agamrossen/VolAnti/assets/field/104m-unit.jpg

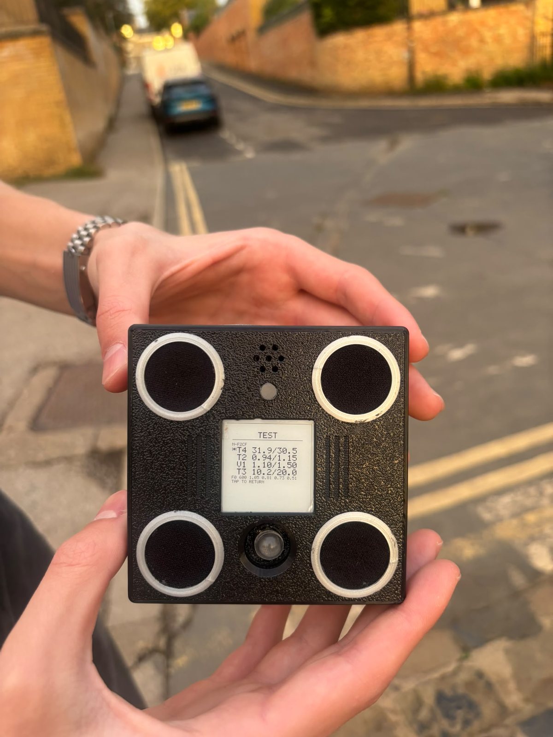
assets/field/104m-unit.jpg
