agamrossen/VolAnti/docs/images/boards-batch.jpg

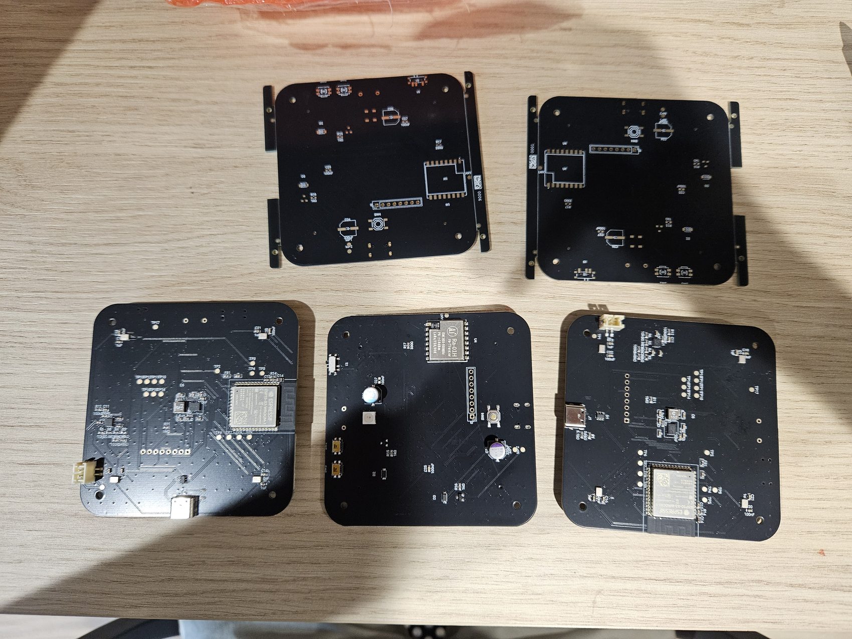
docs/images/boards-batch.jpg
