agamrossen/VolAnti/docs/images/exploded-iso.png

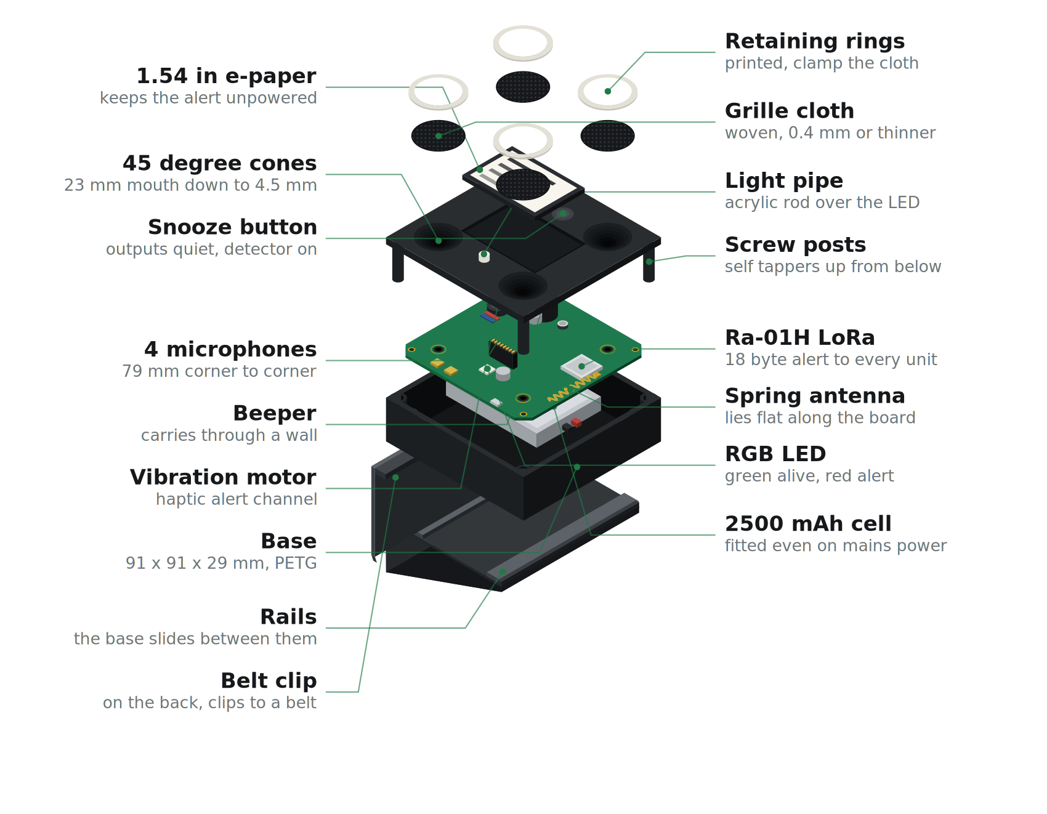
docs/images/exploded-iso.png
