agamrossen/VolAnti/docs/images/hero.jpg

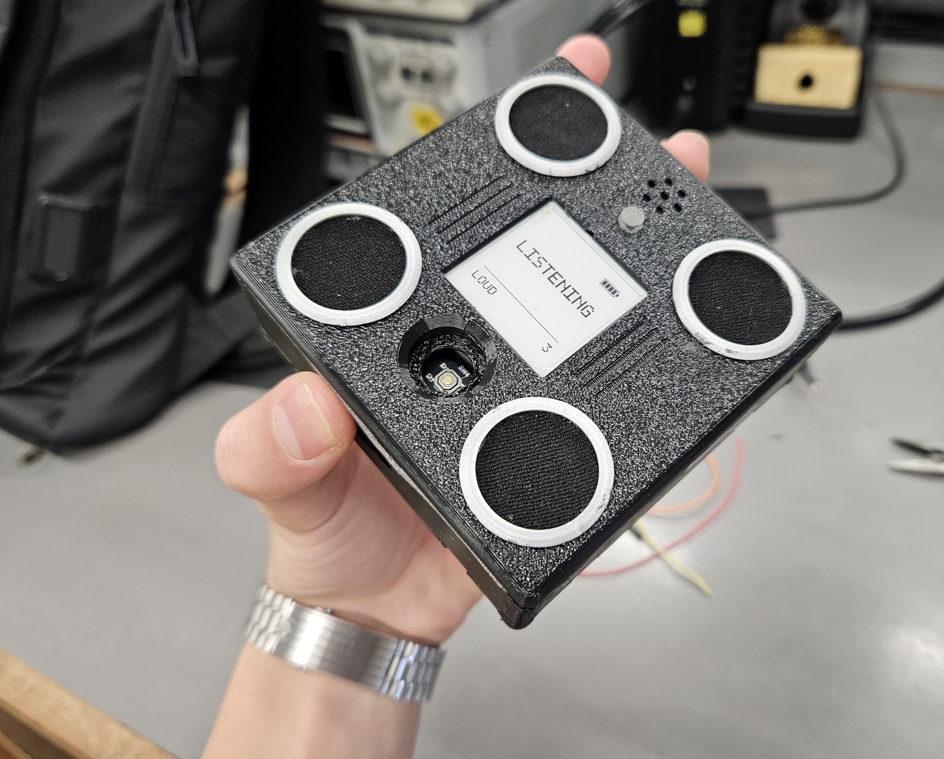
docs/images/hero.jpg
