agamrossen/VolAnti/docs/images/pcb-hand.jpg

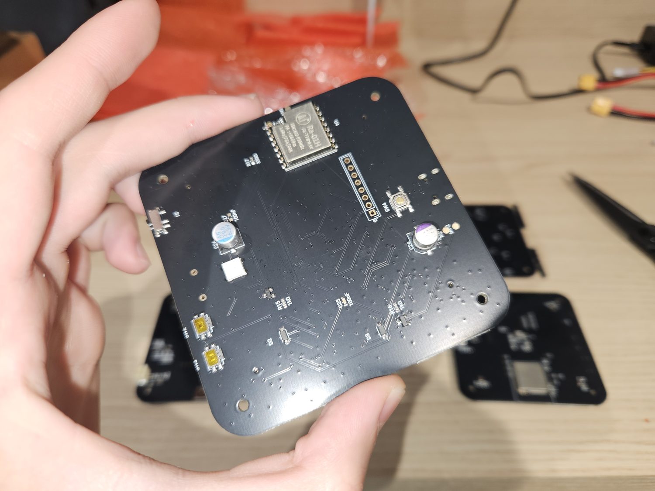
docs/images/pcb-hand.jpg
