agamrossen/VolAnti/firmware/sentry_node/assets/preview_alert.png

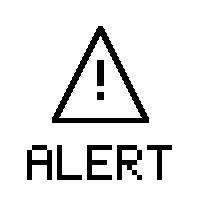
firmware/sentry_node/assets/preview_alert.png
