agamrossen/VolAnti/firmware/sentry_node/assets/preview_alert_wash.png

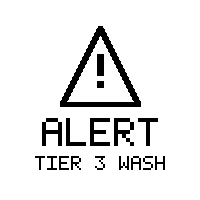
firmware/sentry_node/assets/preview_alert_wash.png
