agamrossen/VolAnti/firmware/sentry_node/assets/preview_listening.png

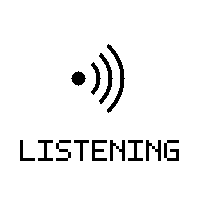
firmware/sentry_node/assets/preview_listening.png
