agamrossen/VolAnti/firmware/sentry_node/assets/preview_listening_footer.png

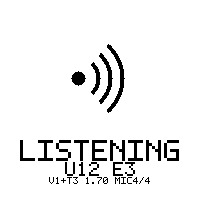
firmware/sentry_node/assets/preview_listening_footer.png
