agamrossen/VolAnti/firmware/sentry_node/assets/preview_listening_footer_rot90.png

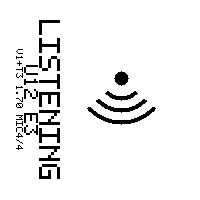
firmware/sentry_node/assets/preview_listening_footer_rot90.png
