agamrossen/VolAnti/firmware/sentry_node/assets/preview_off.png

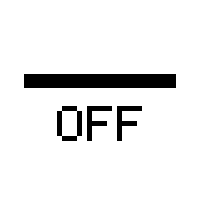
firmware/sentry_node/assets/preview_off.png
