agamrossen/VolAnti/firmware/sentry_node/assets/preview_ready.png

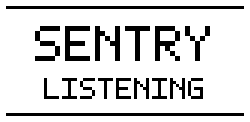
firmware/sentry_node/assets/preview_ready.png
