agamrossen/VolAnti/firmware/sentry_node/assets/preview_rot90_alert.png

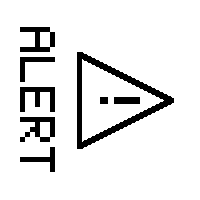
firmware/sentry_node/assets/preview_rot90_alert.png
