agamrossen/VolAnti/firmware/sentry_node/assets/preview_rot90_off.png

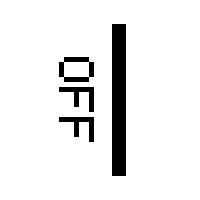
firmware/sentry_node/assets/preview_rot90_off.png
