agamrossen/VolAnti/hardware/enclosure/renders/VolAnti_Base.png

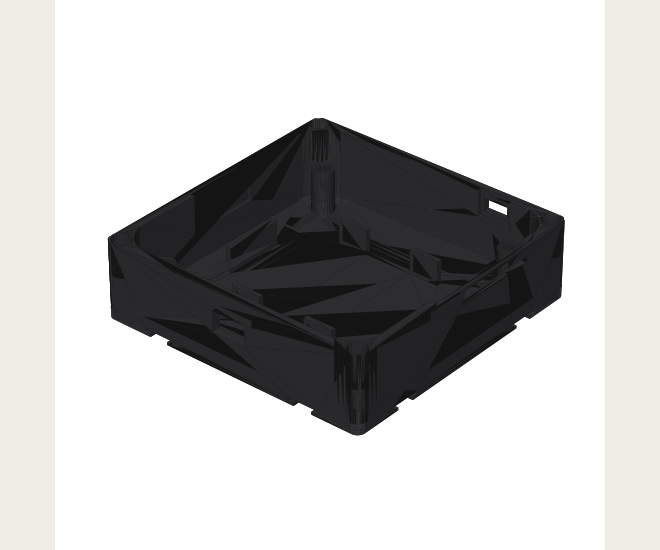
hardware/enclosure/renders/VolAnti_Base.png
