agamrossen/VolAnti/hardware/enclosure/renders/VolAnti_Lid.png

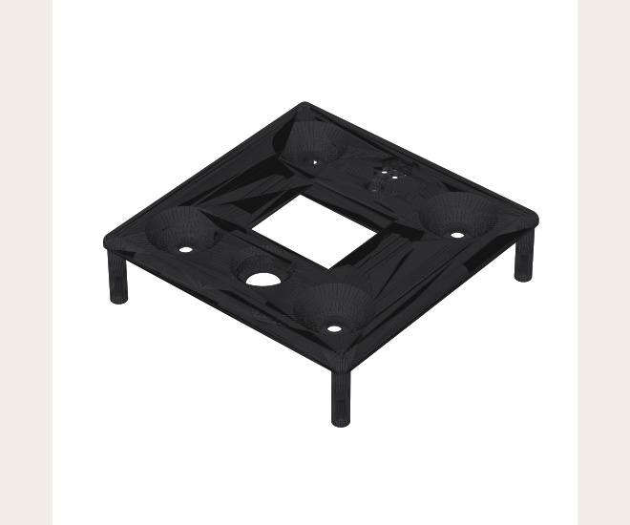
hardware/enclosure/renders/VolAnti_Lid.png
