agamrossen/VolAnti/hardware/enclosure/renders/VolAnti_Mount.png

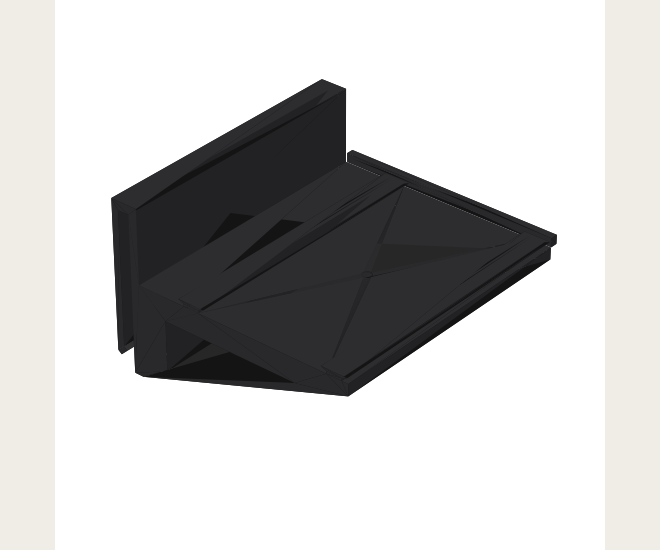
hardware/enclosure/renders/VolAnti_Mount.png
