agamrossen/VolAnti/firmware/sentry_node/assets/preview_rot90_test.png

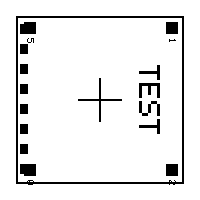
firmware/sentry_node/assets/preview_rot90_test.png
