agamrossen/VolAnti/firmware/sentry_node/assets/preview_test.png

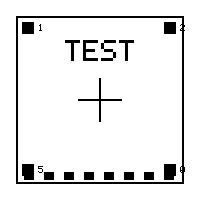
firmware/sentry_node/assets/preview_test.png
