agamrossen/VolAnti/firmware/sentry_node/main/sentry_node.c

/*
 * sentry_node.c - the frame loop, the modes, and the console.
 *
 * For the golden replay the device holds the vectors and the detector and
 * nothing else. It does not hold the expected outcomes: those live in
 * data/golden_vectors.json and are applied by the host comparator, because
 * firmware that knows the answer cannot be said to have reproduced it.
 *
 * Host protocol (line commands in, binary records out):
 *     I                       identity / sizes / free heap, as text
 *     R <idx>                 replay vector idx, stream the trace
 *     P <idx> <from> <to>     ... and interleave forensic probe records
 * Every run emits: header, one record per frame, sentinel.
 */

#include <stdio.h>
#include <stdlib.h>
#include <string.h>

#include "esp_heap_caps.h"
#include "esp_log.h"
#include "esp_sleep.h"
#include "esp_system.h"
#include "esp_timer.h"
#include "freertos/FreeRTOS.h"
#include "freertos/task.h"

#include <math.h>

#include "dsps_fft2r.h"
#include "dsps_fft4r.h"

#include "driver/gpio.h"
#include "driver/rtc_io.h"
#include "esp_adc/adc_cali.h"
#include "esp_adc/adc_cali_scheme.h"
#include "esp_adc/adc_oneshot.h"

#include "actuators.h"
#include "alert_ui.h"
#include "board_pins.h"
#include "boot_rec.h"
#include "combiners_cx.h"
#include "detector.h"
#include "detector_t2.h"
#include "detector_t3.h"
#include "detector_t4.h"
#include "epaper.h"
#include "epaper_draw.h"
#include "ui_config.h"
#include "event_log.h"
#include "settings.h"
#include "led_ws2812.h"
#include "lora_link.h"
#include "mic_cal.h"
#include "nf_probe.h"
#include "power_mon.h"
#include "source.h"
#include "source_i2s_quad.h"
#include "trace.h"

static detector_state_t *g_st;
static detector_work_t  *g_w;
/* The mono staging pair, and why it is not allocated at boot.
 *
 * 12 KB: one n_fft window of float32 and one of int16. Only the mono modes
 * touch it - the golden replay, the meter, the tone check, the self-tests -
 * and the quad pipeline has its own per-channel windows and never reads
 * either.
 *
 * Held for the life of the device it is free only while nothing else is
 * competing: the quad guard needs 70 KB, Tier-2 24 KB, Tier-3 13 KB and the
 * two I2S buses take 48 KB of DMA, and 12 KB held for a mode that is not
 * running is the difference between Tier-3 fitting and the guard refusing to
 * start. So it is allocated lazily and handed back when the guard starts. */
static float            *g_block;      /* sliding window, n_fft float32 */
static int16_t          *g_q;          /* int16 staging, n_fft */

static bool mono_alloc(void)
{
    if (!g_block) {
        g_block = heap_caps_calloc(CFG_N_FFT, sizeof(float),
                                   MALLOC_CAP_INTERNAL | MALLOC_CAP_8BIT);
    }
    if (!g_q) {
        g_q = heap_caps_calloc(CFG_N_FFT, sizeof(int16_t),
                               MALLOC_CAP_INTERNAL | MALLOC_CAP_8BIT);
    }
    if (g_block && g_q) {
        return true;
    }
    trace_text("ERR out of RAM for the mono staging buffers\n");
    return false;
}

static void mono_free(void)
{
    free(g_block);
    g_block = NULL;
    free(g_q);
    g_q = NULL;
}

/* One line of heap truth. Printed when a run starts and when one cannot. */
static void heap_line(const char *what)
{
    char b[96];
    snprintf(b, sizeof(b), "heap %s: free=%u largest=%u\n", what,
             (unsigned)heap_caps_get_free_size(MALLOC_CAP_INTERNAL),
             (unsigned)heap_caps_get_largest_free_block(MALLOC_CAP_INTERNAL));
    trace_text(b);
}

static int cmp_u32(const void *a, const void *b)
{
    uint32_t x = *(const uint32_t *)a, y = *(const uint32_t *)b;
    return (x > y) - (x < y);
}

/* x = q / 32767.0f, exactly as make_golden.py quantised it - 32767, not
 * 32768 - and computed in float32, because numpy's `q.astype(np.float32) /
 * 32767.0` is a float32 operation under NEP 50 weak-scalar promotion. */
static inline float q_to_f(int16_t q)
{
    return (float)q / 32767.0f;
}

/* ==========================================================================
 * One frame loop, four modes. The golden replay and the live microphone run
 * the same code over the same source_read() abstraction; if they did not, the
 * golden evidence would say nothing about the live path, which is the whole
 * point of having the abstraction.
 *
 * The only per-mode differences are which records are emitted and when the
 * loop stops. Nothing mode-specific touches the detector.
 * ========================================================================== */

/* ==========================================================================
 * Tier-2. Everything below is opt-in and reached only through the `H` and
 * `K` letters.
 *
 * The rule that makes it safe: `guard_t2_opts_t *t2o == NULL` is the
 * tier-free behaviour, and every Tier-2 line inside run_quad_pipeline is
 * inside an `if (t2o ...)`. `G` and `Z` pass NULL, so their path through the
 * loop carries the same instructions it would with no Tier-2 in the tree,
 * which is why the golden gate still says what it says.
 * ========================================================================== */
typedef struct {
    bool     enable;
    t2_cfg_t cfg;
    char     cx;              /* 'a' (default) | 'b' | 'c' | 'd' */
    float    f_split_hz;      /* CX-C only */
    float    busoff;          /* CX-D only, samples of bus-B lag */
} guard_t2_opts_t;

/* The runtime exclusion list, set by `E` and consumed by `H`/`K`. Module
 * scope because it must SURVIVE between commands - the operator types it once
 * after a quiet baseline and then runs the guard. */
static int    g_excl_n;
static double g_excl_c[T2_MAX_EXCL];
static double g_excl_t[T2_MAX_EXCL];

static t2_state_t *g_t2st;
static t2_work_t  *g_t2w;
static cx_work_t  *g_cxw;

/* ==========================================================================
 * Tier-3, the wash tier.
 *
 * v1 and Tier-2 search 200-800 Hz for a harmonic comb. The only real propeller
 * this project has recorded put +0.3 dB there and +14.9 dB above 3.2 kHz, and
 * both comb tiers raised zero events on it at 4 m and at 10 m. Tier-3
 * demodulates the high band and finds the blade-pass periodicity in the
 * envelope; on that same audio it latched 94% of the 4 m capture. It is the
 * only tier here that has detected a real rotor.
 *
 * What is wrong with it, equally plainly: it fires on box fans, HVAC
 * condensers, insects, tracked vehicles and helicopters, because a fan and a
 * rotor are the same machine and the statistic cannot separate them. Its
 * calibration failed - the best weighted false-alarm rate reachable at any
 * threshold was 4.87/h against an allowance of 0.40/h - which is why
 * T3_ENABLED_DEFAULT is 0 in the generated header and the no-regression
 * certificate asserts it.
 *
 * It is enabled at runtime rather than in the header, so the sealed artifacts
 * stay untouched and a typed argument or a persisted setting turns it on. The
 * standing rule is that miss cost far exceeds false-alarm cost. Expect
 * nuisance alarms outdoors - that expectation is measured, not speculative -
 * and read the tier field on every alert before believing any of them.
 * ========================================================================== */
typedef struct {
    bool     enable;
    t3_cfg_t cfg;
} guard_t3_opts_t;

/* ==========================================================================
 * Tier-4, the slow comb. Same contract as Tier-3: additive, opt-in, and
 * disabled in the generated header.
 *
 * It is not disabled because it failed. tau4 = 30.5 gives zero events on
 * every real drone-free recording this project owns - 487 s of it, indoor and
 * outdoor - while both real in-band positives fire, the first at 4.45 s. What
 * it does not have is hours. Zero events in 487 s bounds the false-alarm rate
 * at 22/h with 95% confidence against an allowance of 0.40/h, so turning it
 * on in the field means shipping a tier whose false-alarm rate is unmeasured
 * to within a factor of fifty.
 *
 * Until those hours exist it runs on demand, its verdict goes in the trace and
 * the event ring beside the other three, and nothing about the alarm depends
 * on it.
 * ========================================================================== */
typedef struct {
    bool     enable;
    t4_cfg_t cfg;
} guard_t4_opts_t;

static t4_state_t *g_t4st;

static t3_state_t *g_t3st;

/* Tier-3's state is claimed early rather than per-run, and the reason is
 * placement rather than lifetime.
 *
 * t3_state_t is 12688 bytes and must be contiguous. By the time a run has
 * started two I2S buses (48 KB taken as twenty-four separate 2 KB descriptor
 * buffers), the guard (70 KB) and Tier-2 (24 KB), the heap holds 18616 bytes
 * free in no block larger than 7680 - so the allocation fails with plenty of
 * total memory left. Claiming it out of a pristine heap costs the mono modes
 * 12.7 KB they have to spare and removes the failure entirely.
 *
 * Nothing about it is per-run: t3_reset() clears it at the start of every run,
 * exactly as t2_state_reset() does for a buffer that is reallocated. */
static bool t3_boot_alloc(void)
{
    if (g_t3st) {
        return true;
    }
    if (t3_init() != 0) {
        trace_text("ERR t3_init failed (esp-dsp fft2r for the 1024-pt "
                   "envelope transform)\n");
        return false;
    }
    g_t3st = heap_caps_calloc(1, sizeof(t3_state_t),
                              MALLOC_CAP_INTERNAL | MALLOC_CAP_8BIT);
    return g_t3st != NULL;
}

/* Release it again when the configured pair does not include Tier-3.
 *
 * Holding Tier-3's 12688 bytes permanently makes the v1 + Tier-2 pair
 * unallocatable: Tier-2 asks for 15924 with 20720 free and 10752 in the
 * largest block, so the device falls back to v1 alone and the calibrated pair
 * becomes unreachable.
 *
 * So the claim follows the configuration rather than the boot. It is still
 * taken from a pristine heap - reconciled in run_standalone() before the I2S
 * buses and the guard buffers fragment anything - which is the property that
 * matters; what changes is that a pair which does not want it does not pay
 * for it. */
static void t3_free(void)
{
    free(g_t3st);
    g_t3st = NULL;
}

static bool t3_alloc(void) { return g_t3st != NULL; }

static void t4_free(void)
{
    free(g_t4st);
    g_t4st = NULL;
}

/* Idempotent, and claimed from the same pristine heap as the others. ~10 KB,
 * almost all of it the four sub-block accumulators. */
static bool t4_alloc(void)
{
    if (!g_t4st) {
        g_t4st = heap_caps_calloc(1, sizeof(t4_state_t),
                                  MALLOC_CAP_INTERNAL | MALLOC_CAP_8BIT);
    }
    return g_t4st != NULL;
}

static void t2_free(void)
{
    free(g_t2st);
    g_t2st = NULL;
    free(g_t2w);
    g_t2w = NULL;
    free(g_cxw);
    g_cxw = NULL;
}

/* Idempotent, so the same function serves the boot reservation and the lab
 * modes that start a run without one. ~24 KB in two blocks - a t2_work_t is
 * 15924 bytes on its own, and that single block is what fails whenever Tier-2
 * cannot start - plus ~8 KB more only if a non-default combiner is selected.
 *
 * When it is called matters more than what it asks for. Called after the I2S
 * buses and the guard buffers, the 15924 has to come out of a heap already
 * cut into pieces by a 32800-byte spectra block and two DMA rings, and it does
 * not fit with 20720 bytes still free. run_standalone() calls this before any
 * of that; see the reservation block there. */
static bool t2_alloc(bool need_cx)
{
    if (!g_t2st) {
        g_t2st = heap_caps_calloc(1, sizeof(t2_state_t),
                                  MALLOC_CAP_INTERNAL | MALLOC_CAP_8BIT);
    }
    if (!g_t2w) {
        g_t2w = heap_caps_calloc(1, sizeof(t2_work_t),
                                 MALLOC_CAP_INTERNAL | MALLOC_CAP_8BIT);
    }
    if (need_cx && !g_cxw) {
        g_cxw = heap_caps_calloc(1, sizeof(cx_work_t),
                                 MALLOC_CAP_INTERNAL | MALLOC_CAP_8BIT);
        if (!g_cxw) {
            return false;
        }
    }
    return g_t2st && g_t2w;
}

typedef struct {
    const char *name;
    uint32_t n_samples;      /* 0 = unbounded (live) */
    uint32_t max_frames;     /* 0 = unbounded (live) */
    uint32_t prb_from, prb_to;
    bool     emit_pcm;       /* parity: stream the samples too */
    bool     emit_alert;     /* live/parity: one record on the firing frame */
    bool     stop_on_input;  /* live: any host byte ends the run */
    bool     armed;          /* A mode: drive the actuators from rec.fired */
    /* Opt-in. NULL - which every call site that uses designated initialisers
     * leaves it - is exactly the behaviour with no Tier-2 in the tree. Only
     * `K` sets it. */
    const guard_t2_opts_t *t2;
} stream_opts_t;

/* ---- HOW A STANDALONE RUN IS INTERRUPTED --------------------------------
 * A lab mode stops on ANY host byte, which is fine when a human is driving it
 * and fatal when the device starts its own guard at power-on: the byte that
 * stops the run is the first letter of the command that wanted to replace it,
 * and eating it turns `R 0` into `0`. So a standalone run stops on a WHOLE
 * LINE, which is parked here and dispatched by the main loop untouched. */
static char g_pending[64];
static bool g_have_pending;

/* `S` asks the device to hand itself back to the guard. It has to be honoured
 * from both paths - the console loop, and the line that interrupted a
 * standalone run. Handled in only the first, sending `S` to a device that is
 * already guarding stops the guard, routes the line to dispatch_line() and
 * answers with an unknown-command error, leaving the box in the console doing
 * nothing at all. */
static bool g_want_standalone;

/* Why a run ended. The main loop needs to tell "the host wants the console"
 * from "the operator held the button down". */
#define RUN_END_INPUT     0     /* a host line is waiting in g_pending      */
/* The off ritual: a hold. It draws OFF with the reason under it and then
 * deep-sleeps, or parks on a board that cannot, so the cable can be pulled -
 * or the PCB's slider thrown - against a screen that is telling the truth.
 *
 * There is exactly one ending. Parking in standby with the panel still saying
 * LISTENING is the failure the ritual exists to remove, and a tap-count ritual
 * cannot coexist with paging, since three taps is how an operator reads three
 * pages. */
#define RUN_END_POWER     1     /* the two-second hold                      */
#define RUN_END_COMPLETE  2     /* ran to its length, or could not start    */
/* The cell ran out. Kept apart from RUN_END_POWER because the two lead to
 * different words on the same screen: one is an operator putting the device
 * away, the other is a device that must not come straight back up and finish
 * the battery off. */
#define RUN_END_BATTERY   3

static inline uint32_t now_ms(void)
{
    return (uint32_t)(esp_timer_get_time() / 1000);
}

/* ---- console-transparent commands ---------------------------------------
 *
 * Any host line takes the console and stops the guard. That is deliberate,
 * because a lab session must be deterministic - but it makes two commands
 * impossible to use for what they exist for. `U btn` cannot drive the state
 * machine if the line carrying it stops the machine, and the frame-budget gate
 * needs an alert to land while four tiers are running.
 *
 * So exactly two prefixes are handled in the reader and never reach the
 * take-over. They are the two that act on the running guard rather than
 * asking it to stand down. Everything else takes the console. */
static const char *skip_ws(const char *p);
static void info_publish(int alive, int amb_db, const char *amb_word);
static void test_publish(void);
static void test_console_line(void);
static void frozen_publish(void);
static bool cmd_btn_word(const char *args);
static bool cmd_alert_word(const char *args);

static bool run_transparent_line(const char *line)
{
    const char *a = skip_ws(line);
    if (*a != 'U' && *a != 'u') {
        return false;
    }
    a = skip_ws(a + 1);
    if (!strncmp(a, "btn", 3)) {
        return cmd_btn_word(skip_ws(a + 3));
    }
    if (!strncmp(a, "alert", 5)) {
        return cmd_alert_word(skip_ws(a + 5));
    }
    return false;
}

/* The one place a long run decides to end. Standalone runs consume a whole
 * line and park it; lab runs stop on any byte. */
static bool run_should_stop(bool standalone, bool armed, int *reason)
{
    if (armed && alert_ui_power_off_requested()) {
        *reason = RUN_END_POWER;
        return true;
    }
    /* The rotation an operator just asked for, persisted. Polled beside the
     * power request because they are the same kind of event: a hold on the
     * button that the UI has already acted on and that something outside the
     * UI has to finish. The panel has already turned; this only writes the
     * quadrant to NVS so it survives the next power cycle, which is the whole
     * point of being able to do it without a laptop. Settings deliberately do
     * not reach into alert_ui.c, so the write lives here. */
    if (alert_ui_take_rotation()) {
        settings_mut()->epd_rotation = epaper_get_rotation();
        const bool ok = settings_save();
        char rb[96];
        snprintf(rb, sizeof(rb), "ROT %u deg %s\n",
                 (unsigned)epaper_degrees_from_quadrant(epaper_get_rotation()),
                 ok ? "saved" : "NOT SAVED");
        trace_text(rb);
    }
    /* The cell, checked here beside the button because they are the same kind
     * of event: something outside the detector has decided the run is over.
     * Reading it is a volatile byte load - the measurement happens on the
     * power task, on the other core, once every ten seconds. Inert on any
     * board with no divider, where power_mon_state() returns POWER_OK. */
    if (armed && power_mon_state() == POWER_EMPTY) {
        *reason = RUN_END_BATTERY;
        return true;
    }
    if (standalone) {
        if (trace_try_line(g_pending, sizeof(g_pending)) > 0) {
            /* Handled here and the guard keeps running: see
             * run_transparent_line. */
            if (run_transparent_line(g_pending)) {
                return false;
            }
            g_have_pending = true;
            *reason = RUN_END_INPUT;
            return true;
        }
        return false;
    }
    if (trace_poll_byte() >= 0) {
        *reason = RUN_END_INPUT;
        return true;
    }
    return false;
}

static void run_stream(source_t *src, const stream_opts_t *o)
{
    trace_hdr_t h = {
        .magic = TRACE_MAGIC_HDR, .version = TRACE_VERSION,
        .n_samples = o->n_samples, .n_frames = o->max_frames,
        .threshold = src->thr,   /* the source's own preset, not a global */
        .fs = CFG_FS, .n_fft = CFG_N_FFT, .hop = CFG_HOP,
        .n_bins = CFG_N_BINS, .n_f0 = CFG_N_F0,
        .rec_size = sizeof(trace_rec_t),
    };
    strncpy(h.name, o->name, sizeof(h.name) - 1);
    trace_send_hdr(&h);

    detector_state_reset(g_st, src->thr);
    /* The golden vectors test the sealed detector and nothing else.
     * detector_state_reset() memsets, so trk_family and veto_voice are clear
     * here whatever the operator has stored in settings, and the vectors are
     * replayed against exactly the code they were cut from. That is true only
     * as a side effect of the memset, so: do not copy the settings flags into
     * g_st on this path. A gate that judges a different detector from the one
     * it was calibrated against proves nothing. */
    g_st->trk_family = false;
    g_st->veto_voice = false;
    g_st->nf_gate    = false;   /* same reason */
    const bool t2on = (o->t2 != NULL && o->t2->enable);
    if (t2on) {
        t2_state_reset(g_t2st);
    }
    uint8_t prev_fired2 = 0;
    uint32_t t2_hits_total = 0;

    const bool bounded = (o->max_frames != 0);
    uint32_t *us = bounded ? calloc(o->max_frames, sizeof(uint32_t)) : NULL;
    uint64_t total_us = 0;
    uint32_t max_us = 0, n_fast = 0;
    uint64_t us_fft = 0, us_mag = 0, us_floor = 0, us_score = 0;
    float peak = -1e30f;
    int32_t longest = 0;
    double t_last = 0.0;
    uint32_t i = 0;
    uint8_t prev_fired = 0;
    uint32_t pcm_seq = 0, sample_index = 0;

    for (i = 0; !bounded || i < o->max_frames; i++) {
        /* slide the analysis window: frame i is x[i*hop : i*hop + n_fft] */
        const int want = (i == 0) ? CFG_N_FFT : CFG_HOP;
        if (i != 0) {
            memmove(g_block, g_block + CFG_HOP,
                    (CFG_N_FFT - CFG_HOP) * sizeof(float));
        }
        if (source_read(src, g_q, (size_t)want) != want) {
            break;                   /* stream ended, or the mic stopped */
        }
        float *dst = (i == 0) ? g_block : g_block + (CFG_N_FFT - CFG_HOP);
        for (int k = 0; k < want; k++) {
            dst[k] = q_to_f(g_q[k]);
        }
        if (o->emit_pcm) {
            /* Emitted before the trace record derived from it, and including
             * the whole first window, so the host can reconstruct exactly the
             * sample array the detector saw - x[0 : n_fft + (frames-1)*hop]. */
            trace_send_pcm(pcm_seq++, sample_index, g_q, (uint16_t)want);
        }
        sample_index += (uint32_t)want;

        /* frame END time - causal, exactly as detector.py computes it */
        const double t = (double)(i * CFG_HOP + CFG_N_FFT) / (double)CFG_FS;
        frame_rec_t rec;

        const int64_t c0 = esp_timer_get_time();
        front_end(g_block, g_w->spec[0], g_w);
        const cf32_t *sp = combiner(&g_w->spec[0][0], CFG_N_CHANNELS, g_w);
        const int64_t cf = esp_timer_get_time();
        back_end(sp, g_st, t, i, g_w, &rec);
        const int64_t c1 = esp_timer_get_time();
        us_fft += (uint64_t)(cf - c0);
        us_mag += rec.us_mag;
        us_floor += rec.us_floor;
        us_score += rec.us_score;

        const uint32_t dt = (uint32_t)(c1 - c0);
        if (us) {
            us[i] = dt;
        }
        total_us += dt;
        if (dt > max_us) {
            max_us = dt;
        }
        if (rec.score > peak) {
            peak = rec.score;
        }
        if (rec.chain > longest) {
            longest = rec.chain;
        }
        n_fast += rec.floor_fast;
        t_last = t;

        trace_rec_t r = {
            .magic = TRACE_MAGIC_REC,
            .frame = rec.frame, .t_s = rec.t_s, .score = rec.score,
            .f0_bin = rec.f0_bin, .f0_hz = rec.f0_hz,
            .f0_raw_hz = rec.f0_raw_hz, .teeth = rec.teeth,
            .floor_fast = rec.floor_fast, .reanch = rec.reanch,
            .n_held_bins = rec.n_held_bins, .above_thr = rec.above_thr,
            .cont_accepted = rec.cont_accepted, .chain = rec.chain,
            .fired = rec.fired, .is_octave = rec.is_octave,
            .us_frame = dt,
        };
        trace_send_rec(&r);

        if (o->emit_alert && rec.fired && !prev_fired) {
            trace_alt_t a = {.magic = TRACE_MAGIC_ALT, .frame = i,
                             .t_s = t, .f0_hz = rec.f0_hz,
                             .score = rec.score, .chain = rec.chain,
                             .n_events = (uint32_t)g_st->n_events + 1u};
            trace_send_alt(&a);
        }
        prev_fired = rec.fired;

        /* Tier-2 beside the sealed tier, on the same spectrum, in `K` mode
         * only. It reads `sp` after back_end has finished with it and writes
         * nothing v1 can see, which is why `R` and `K` produce identical v1
         * records for the same vector. */
        if (t2on) {
            t2_rec_t t2r;
            if (t2_step(sp, NULL, 1, &o->t2->cfg, g_t2st, t, i, g_t2w, &t2r)) {
                trace_t2r_t tr = {
                    .magic = TRACE_MAGIC_T2R, .frame = t2r.frame,
                    .t_s = t2r.t_s, .score2 = t2r.score2,
                    .f02_hz = t2r.f02_hz, .f02_row = t2r.f02_row,
                    .teeth2 = t2r.teeth2, .hit = t2r.hit,
                    .fired2 = t2r.fired2, .excluded = t2r.excluded,
                    .hits = t2r.hits, .n2 = t2r.n2,
                    .track_age = t2r.track_age, .kappa = t2r.kappa,
                    .us_t2 = t2r.us_t2};
                trace_send_t2r(&tr);
                t2_hits_total += t2r.hit;
                if (t2r.fired2 && !prev_fired2) {
                    trace_al2_t a2 = {
                        .magic = TRACE_MAGIC_AL2, .frame = i, .t_s = t,
                        .f02_hz = g_t2st->f0_on, .score2 = t2r.score2,
                        .hits = t2r.hits, .kappa = t2r.kappa,
                        .n_events = (uint32_t)g_t2st->n_events + 1u};
                    trace_send_al2(&a2);
                }
                prev_fired2 = t2r.fired2;
            }
        }

        /* The entire armed-mode integration: one O(1) call, reading a flag
         * the detector already computed. It cannot influence front_end,
         * combiner, back_end or their inputs, and it is skipped entirely in
         * every other mode, which is why `L` remains a valid timing comparator
         * for `A`. */
        if (o->armed) {
            alert_ui_tick(rec.fired != 0, ALERT_TIER_V1, now_ms());
        }

        if (i >= o->prb_from && i <= o->prb_to) {
            probe_rec_t p;
            detector_probe(g_w, g_st, &rec, &p);
            trace_prb_t tp = {.magic = TRACE_MAGIC_PRB, .frame = i,
                              .win_checksum = window_checksum(g_w->fftbuf,
                                                              CFG_N_FFT),
                              .e = p.e, .e_slow = p.e_slow, .flat = p.flat,
                              .rising = p.rising, .fast = p.fast,
                              .argmax_bin = p.argmax_bin,
                              .argmax_score = p.argmax_score};
            memcpy(tp.probe_bin, p.probe_bin, sizeof(tp.probe_bin));
            memcpy(tp.probe_mag, p.probe_mag, sizeof(tp.probe_mag));
            memcpy(tp.probe_floor, p.probe_floor, sizeof(tp.probe_floor));
            memcpy(tp.probe_S, p.probe_S, sizeof(tp.probe_S));
            trace_send_prb(&tp);
        }

        if (o->stop_on_input && trace_poll_byte() >= 0) {
            i++;
            break;
        }
    }

    detector_finish(g_st, t_last);
    if (t2on) {
        t2_finish(g_t2st, t_last);
        char b[80];
        snprintf(b, sizeof(b), "T2 events=%u hits=%u\n",
                 (unsigned)g_t2st->n_events, (unsigned)t2_hits_total);
        trace_text(b);
    }

    const uint32_t n_done = i;
    uint32_t p99 = 0;
    if (us && n_done) {
        qsort(us, n_done, sizeof(uint32_t), cmp_u32);
        uint32_t k = (uint32_t)((99 * n_done + 99) / 100);   /* ceil(0.99n) */
        if (k == 0) {
            k = 1;
        }
        p99 = us[k - 1];
    }
    free(us);

    trace_end_t e = {
        .magic = TRACE_MAGIC_END, .n_frames = n_done,
        .verdict_fires = (g_st->n_events > 0) ? 1 : 0,
        .n_events = (uint32_t)g_st->n_events,
        .peak_score = peak, .longest_chain = longest,
        .n_floor_fast = n_fast, .n_reanch = 0, .n_held_frames = 0,
        .total_us = total_us, .max_us = max_us, .p99_us = p99,
        .us_fft = us_fft, .us_mag = us_mag, .us_floor = us_floor,
        .us_score = us_score,
        .chain_overflow = g_st->overflow ? 1 : 0,
    };
    trace_send_end(&e);
}

/* ---- mode: golden - the parity build ----------------------------------- */
static void run_vector(int idx, uint32_t prb_from, uint32_t prb_to)
{
    if (!mono_alloc()) {
        return;
    }
    source_t src;
    if (source_golden(&src, idx) != ESP_OK) {
        trace_text("ERR bad vector index\n");
        return;
    }
    const uint32_t n = src.n_total;
    const stream_opts_t o = {
        .name = src.name, .n_samples = n,
        .max_frames = (n < CFG_N_FFT) ? 0u : 1u + (n - CFG_N_FFT) / CFG_HOP,
        .prb_from = prb_from, .prb_to = prb_to,
    };
    if (o.max_frames == 0) {
        trace_text("ERR vector shorter than one window\n");
        return;
    }
    run_stream(&src, &o);
}

/* ---- mode: K - golden vector i, with Tier-2 running beside it -----------
 *
 * Replays the same vector from the same flash array through the same
 * run_stream at the vector's own preset threshold, so the v1 half of a `K`
 * trace is byte-identical to the `R` trace for the same index - and the
 * comparator checks exactly that before it looks at Tier-2 at all. The
 * addition is the T2R stream, diffed against src/detector_t2.py run on the
 * same flash-resident samples.
 *
 * `R` is not modified and no new flash vector is added: the four that exist
 * exercise Tier-2's floor, score and tracker perfectly well.
 *
 * kappa is 1.0 on every frame here by definition rather than by omission -
 * one microphone has nothing to be coherent with.
 */
static void run_vector_t2(int idx, int thr2_milli, int rate)
{
    if (!mono_alloc()) {
        return;
    }
    source_t src;
    if (source_golden(&src, idx) != ESP_OK) {
        trace_text("ERR bad vector index\n");
        trace_ack("K", TRACE_ACK_BAD_ARG);
        return;
    }
    const uint32_t n = src.n_total;
    if (n < CFG_N_FFT) {
        trace_text("ERR vector shorter than one window\n");
        trace_ack("K", TRACE_ACK_BAD_ARG);
        return;
    }
    if (!t2_alloc(false)) {
        t2_free();
        trace_text("ERR t2 out of RAM\n");
        trace_ack("K", TRACE_ACK_FAULT);
        return;
    }
    guard_t2_opts_t o2 = {0};
    o2.enable = true;
    o2.cx = 'a';
    t2_cfg_default(&o2.cfg,
                   rate == 1 ? false
                             : (rate == 2 ? true : (T2_HALF_RATE_DEFAULT != 0)));
    t2_cfg_set_thr_milli(&o2.cfg, thr2_milli);
    if (g_excl_n > 0) {
        t2_cfg_set_excl(&o2.cfg, g_excl_n, g_excl_c, g_excl_t);
    }

    char b[128];
    snprintf(b, sizeof(b),
             "K %s tau2_milli=%d N2=%d M2=%d rate=%s\n", src.name,
             (int)(o2.cfg.tau2 * 1000.0 + 0.5), o2.cfg.n2, o2.cfg.m2,
             o2.cfg.decim == 2 ? "half" : "full");
    trace_text(b);

    const stream_opts_t o = {
        .name = src.name, .n_samples = n,
        .max_frames = 1u + (n - CFG_N_FFT) / CFG_HOP,
        .prb_from = 0xFFFFFFFFu, .prb_to = 0u,
        .t2 = &o2,
    };
    run_stream(&src, &o);
    t2_free();
}

/* ---- mode: live - the detector on the mic, at the deployment default ---- */
static void run_live(void)
{
    if (!mono_alloc()) {
        return;
    }
    source_t src;
    esp_err_t e = source_i2s(&src);
    if (e != ESP_OK) {
        trace_text("ERR i2s init failed\n");
        return;
    }
    const stream_opts_t o = {
        .name = src.name, .n_samples = 0, .max_frames = 0,
        .prb_from = 0xFFFFFFFFu, .prb_to = 0u,
        .emit_alert = true, .stop_on_input = true,
    };
    run_stream(&src, &o);
    source_i2s_stop();
}

/* ---- mode: A - armed live, identical to L plus the actuators ------------
 * Same source, same detector, same threshold, same records. The only
 * difference is `armed`, which enables the one alert_ui_tick() call after
 * back_end. `L` is deliberately left untouched so it stays the reference
 * `A`'s p99 is compared against. */
static void run_armed(void)
{
    if (!mono_alloc()) {
        return;
    }
    source_t src;
    if (source_i2s(&src) != ESP_OK) {
        trace_text("ERR i2s init failed\n");
        trace_ack("A", TRACE_ACK_FAULT);
        return;
    }
    alert_ui_begin('A');
    const stream_opts_t o = {
        .name = src.name, .n_samples = 0, .max_frames = 0,
        .prb_from = 0xFFFFFFFFu, .prb_to = 0u,
        .emit_alert = true, .stop_on_input = true, .armed = true,
    };
    run_stream(&src, &o);
    alert_ui_end();                 /* safe-off is inside */
    source_i2s_stop();
}

/* ---- mode: D - alert drill, no detector, no microphone -----------------
 * Exercises the whole alert/snooze/re-arm loop deterministically so the bench
 * can prove the state machine without needing audio to cooperate. */
static void run_drill(uint32_t seconds)
{
    if (seconds == 0u || seconds > 3600u) {
        seconds = 60u;
    }
    alert_ui_begin('D');

    const uint32_t t0 = now_ms();
    const uint32_t run_ms = seconds * 1000u;
    uint32_t next_trigger_ms = t0;          /* first alert immediately */
    uint32_t trigger_until_ms = 0;
    bool trigger = false;

    for (;;) {
        const uint32_t now = now_ms();
        if ((now - t0) >= run_ms) {
            break;
        }
        if (!trigger && (int32_t)(now - next_trigger_ms) >= 0) {
            trigger = true;
            trigger_until_ms = now + 8000u;   /* 8 s, or until snoozed */
            next_trigger_ms = now + 45000u;   /* then one every 45 s   */
        }
        if (trigger) {
            if ((int32_t)(now - trigger_until_ms) >= 0 ||
                alert_ui_state() == TRACE_ALERT_SNOOZED) {
                trigger = false;
            }
        }
        alert_ui_tick(trigger, ALERT_TIER_V1, now);

        if (trace_poll_byte() >= 0) {
            break;
        }
        vTaskDelay(pdMS_TO_TICKS(20));        /* also the debounce period */
    }

    alert_ui_end();
    trace_end_t e = {.magic = TRACE_MAGIC_END, .n_frames = 0};
    trace_send_end(&e);
}

/* ---- mode: Q - quad meter ----------------------------------------------
 * Per-channel level and per-bus health. On a read timeout this emits a STAT
 * naming the bus and keeps trying: a dead bus must be loudly visible rather
 * than producing the clean instant exit the mono meter gives. */
static int16_t g_quad[QUAD_FRAMES_PER_READ * QUAD_N_CH];

static void run_quad_meter(void)
{
    if (source_i2s_quad_start() != ESP_OK) {
        trace_text("ERR quad i2s init failed\n");
        trace_ack("Q", TRACE_ACK_FAULT);
        return;
    }
    trace_hdr_t h = {
        .magic = TRACE_MAGIC_HDR, .version = TRACE_VERSION,
        .n_samples = 0, .n_frames = 0, .threshold = 0.0,
        .fs = CFG_FS, .n_fft = CFG_N_FFT, .hop = CFG_HOP,
        .n_bins = CFG_N_BINS, .n_f0 = CFG_N_F0,
        .rec_size = sizeof(trace_qmt_t),
    };
    strncpy(h.name, "quad_meter", sizeof(h.name) - 1);
    trace_send_hdr(&h);

    const uint32_t BLOCK = CFG_FS / 2;            /* 500 ms per record */
    uint32_t seq = 0;

    for (;;) {
        int64_t sum[QUAD_N_CH] = {0}, sumsq[QUAD_N_CH] = {0};
        int32_t vmin[QUAD_N_CH], vmax[QUAD_N_CH], peak[QUAD_N_CH] = {0};
        for (int c = 0; c < QUAD_N_CH; c++) {
            vmin[c] = 32767;
            vmax[c] = -32768;
        }
        uint32_t got = 0;
        uint32_t empty_reads = 0;

        while (got < BLOCK) {
            const int n = source_i2s_quad_read_ex(g_quad, true);
            if (n <= 0) {
                /* Loud, and keep going. */
                empty_reads++;
                trace_stat_t s = {0};
                s.magic = TRACE_MAGIC_STA;
                s.mode = 'Q';
                s.uptime_ms = now_ms();
                s.button_level = 1;
                trace_send_stat(&s);
                if (empty_reads >= 10u) {
                    break;             /* emit what we have, then loop again */
                }
                continue;
            }
            for (int f = 0; f < n; f++) {
                for (int c = 0; c < QUAD_N_CH; c++) {
                    const int32_t v = g_quad[f * QUAD_N_CH + c];
                    sum[c] += v;
                    sumsq[c] += (int64_t)v * v;
                    if (v < vmin[c]) { vmin[c] = v; }
                    if (v > vmax[c]) { vmax[c] = v; }
                    const int32_t a = (v < 0) ? -v : v;
                    if (a > peak[c]) { peak[c] = a; }
                }
            }
            got += (uint32_t)n;
        }

        trace_qmt_t m = {.magic = TRACE_MAGIC_QMT, .seq = seq++,
                         .t_us = (uint64_t)esp_timer_get_time(),
                         .n_samples = got};
        for (int c = 0; c < QUAD_N_CH; c++) {
            m.rms[c] = got ? sqrt((double)sumsq[c] / (double)got) : 0.0;
            m.dc[c] = got ? (double)sum[c] / (double)got : 0.0;
            m.peak[c] = peak[c];
            m.vmin[c] = got ? vmin[c] : 0;
            m.vmax[c] = got ? vmax[c] : 0;
        }
        const quad_stats_t *st = source_i2s_quad_stats();
        for (int b = 0; b < QUAD_N_BUS; b++) {
            m.timeouts[b] = st->timeouts[b];
            m.short_reads[b] = st->short_reads[b];
            m.frames_total[b] = st->frames_total[b];
        }
        trace_send_qmt(&m);

        if (trace_poll_byte() >= 0) {
            break;
        }
    }
    trace_end_t e = {.magic = TRACE_MAGIC_END, .n_frames = seq};
    trace_send_end(&e);
    source_i2s_quad_stop();
}

/* ---- mode: X - quad PCM capture ---------------------------------------
 * ~128 kB/s of 4-channel int16 over USB-Serial-JTAG is unproven, which is why
 * every record carries a mandatory sequence number: the host must be able to
 * detect loss exactly and analyse only contiguous stretches, rather than
 * splicing across a gap and reading the splice as an inter-channel delay. */
static void run_quad_capture(uint32_t seconds)
{
    if (source_i2s_quad_start() != ESP_OK) {
        trace_text("ERR quad i2s init failed\n");
        trace_ack("X", TRACE_ACK_FAULT);
        return;
    }
    const uint32_t n_total = seconds * CFG_FS;
    trace_hdr_t h = {
        .magic = TRACE_MAGIC_HDR, .version = TRACE_VERSION,
        .n_samples = n_total, .n_frames = 0, .threshold = 0.0,
        .fs = CFG_FS, .n_fft = CFG_N_FFT, .hop = CFG_HOP,
        .n_bins = CFG_N_BINS, .n_f0 = CFG_N_F0,
        .rec_size = sizeof(trace_pc4_hdr_t),
    };
    strncpy(h.name, "quad_pcm", sizeof(h.name) - 1);
    trace_send_hdr(&h);

    uint32_t seq = 0, base = 0, empty = 0;
    while (base < n_total) {
        const int n = source_i2s_quad_read(g_quad);
        if (n <= 0) {
            empty++;
            trace_stat_t s = {0};
            s.magic = TRACE_MAGIC_STA;
            s.mode = 'X';
            s.uptime_ms = now_ms();
            s.button_level = 1;
            trace_send_stat(&s);
            if (empty >= 25u) {
                break;                 /* a bus is dead; stop rather than spin */
            }
            continue;
        }
        empty = 0;
        trace_send_pcm4(seq++, base, g_quad, (uint16_t)n, QUAD_N_CH);
        base += (uint32_t)n;
        if (trace_poll_byte() >= 0) {
            break;
        }
    }
    trace_end_t e = {.magic = TRACE_MAGIC_END, .n_frames = seq};
    trace_send_end(&e);
    source_i2s_quad_stop();
}

/* ==========================================================================
 * mode: G - GUARD. The whole device, running as a device.
 *
 * Four microphones -> front_end per channel -> combiner (broadside sum) ->
 * the committed back_end at the DEPLOYMENT threshold -> buzzer, motor, LED,
 * e-paper, and a snooze button that silences the outputs without ever gating
 * detection. Runs until the host sends a byte.
 *
 * What the combiner does here: it is the existing N>1 path, an unweighted
 * complex sum across the four spectra. That is a broadside (delay-zero) beam -
 * it favours sound arriving equally at all four capsules and gives roughly
 * +6 dB on a correlated source against uncorrelated noise. It is not steered
 * beamforming and it produces no bearing. Nothing here touches front_end,
 * combiner or back_end themselves.
 *
 * The caveat: every threshold in this project was calibrated on one
 * microphone, and summing four changes the signal-to-floor relationship in a
 * way that has never been measured. The adaptive floor should absorb most of
 * it, since signal and floor scale together, but "should" is not "was
 * measured". Treat guard-mode detections as qualitative until there is a
 * bench measurement.
 * ========================================================================== */
#define GUARD_N_CH QUAD_N_CH

/* Tier-4's telemetry is a text line, on purpose.
 *
 * Every other tier has a binary trace record, and adding a fifth would mean
 * changing trace.h and trace_proto.py - the wire format the golden gate, the
 * quad parity gate and every capture tool already agree on. Tier-4 ships
 * disabled and has no parity gate yet, so a protocol change would spend the
 * thing those gates depend on before there is anything to spend it for.
 *
 * A text line costs nothing: every host parser already skips text, and at
 * 3.9 updates a second a seventy-byte line is 273 B/s. When Tier-4 earns a
 * parity gate it earns a binary record with it, and that is the moment to
 * change the wire.
 *
 * The fields are the reference record's, in its order, so a host diff needs no
 * translation layer. */
static void trace_text_t4(uint32_t frame, const t4_rec_t *r)
{
    char b[224];
    /* The per-stage breakdown rides on the same line. us= alone says how
     * long an update took and not where it went; these four say where, and
     * us_other is the computed remainder so the five visibly sum to us= or
     * the gap is on the line to be argued with. Appended after the existing
     * fields, so every tool that reads the old line still reads it. */
    snprintf(b, sizeof(b),
             "T4R f=%lu t=%.3f W4=%.3f f0=%.1f ratio=%.3f hit=%d above=%d "
             "excl=%d hits=%d/%d age=%d fired=%d us=%lu "
             "psd=%lu prom=%lu scan=%lu track=%lu other=%lu\n",
             (unsigned long)frame, r->t, r->W4, r->f0, r->ratio,
             r->hit ? 1 : 0, r->above ? 1 : 0, r->excluded ? 1 : 0,
             r->hits, r->n4, r->track_age, r->fired4 ? 1 : 0,
             (unsigned long)r->us_t4,
             (unsigned long)r->us_psd, (unsigned long)r->us_prom,
             (unsigned long)r->us_scan, (unsigned long)r->us_track,
             (unsigned long)r->us_other);
    trace_text(b);
}

/* ==========================================================================
 * Frame scheduling - which frames each tier makes expensive.
 *
 * Nothing about the algorithms makes three tiers in one 32 ms hop hard. What
 * makes it hard is that Tier-2 and Tier-3 each have one heavy frame in a
 * repeating cycle, and if the two cycles line up, every heavy frame is heavy
 * twice.
 *
 *   v1, quad          21.7 ms   every frame
 *   Tier-2 step        7.5 ms   every T2 decim-th    (29.2 - 21.7)
 *   Tier-3 transform   9.1 ms   every 4th            (30.8 - 21.7)
 *
 * Disjoint: worst frame ~= 21.7 + 9.1 = 30.8 ms, inside the hop.
 * Collided: worst frame ~= 21.7 + 7.5 + 9.1 = 38.3 ms, and real time is gone.
 *
 * Tier-2's phase: t2_step increments its own frame counter on every call and
 * works when the remainder is zero, so with decim 2 it works on even frames,
 * counting from the first frame of the run.
 *
 * Tier-3's phase: t3_push_block appends T3_HOP/T3_DECIM envelope samples per
 * frame and transforms when it holds T3_ENV_NFFT of them and T3_ENV_HOP are
 * new. The ring has to fill before the first transform, which is
 * T3_PRIME_FRAMES pushes, so the first transform lands on the
 * (T3_PRIME_FRAMES-1)-th frame Tier-3 sees rather than the first. Everything
 * after that is every T3_FRAMES_PER_UPDATE frames, which is even, so the
 * parity of the first transform is the parity of all of them.
 *
 * Starting Tier-3 at frame 0 therefore puts every transform on an odd frame,
 * which is exactly where Tier-2 is not. Delaying it by one frame moves all of
 * them onto even frames instead - the collision such a guard would be written
 * to prevent. The static assertion below is what holds it, because this is
 * arithmetic a comment cannot enforce.
 * ========================================================================== */
#define T3_ENV_PER_FRAME      (T3_HOP / T3_DECIM)
#define T3_FRAMES_PER_UPDATE  (T3_ENV_HOP / T3_ENV_PER_FRAME)
#define T3_PRIME_FRAMES       (T3_ENV_NFFT / T3_ENV_PER_FRAME)
#define T3_START_FRAME        0
#define T3_FIRST_UPDATE_FRAME (T3_START_FRAME + T3_PRIME_FRAMES - 1)

_Static_assert(T3_ENV_HOP % T3_ENV_PER_FRAME == 0,
               "Tier-3's update cadence is not a whole number of frames");
_Static_assert(T3_ENV_NFFT % T3_ENV_PER_FRAME == 0,
               "Tier-3's priming is not a whole number of frames");
_Static_assert(T3_FRAMES_PER_UPDATE % 2 == 0,
               "Tier-3's cadence is odd, so its updates do not keep a parity "
               "and cannot be held off Tier-2's frames by a phase choice");
_Static_assert(T3_FIRST_UPDATE_FRAME % 2 == 1,
               "Tier-3's first transform lands on an EVEN frame, which is "
               "where a half-rate Tier-2 also works. Fix the start frame, do "
               "not delete this assertion.");

/* Tier-4's slot. Same arithmetic, and it is a function in detector_t4.c
 * rather than a sentence because the accumulator has to fill before the first
 * update, so the first update lands on the (T4_WIN_FRAMES-1)-th frame Tier-4
 * sees. With three tiers there are three cycles to keep apart:
 *
 *   Tier-2   every 2nd frame          -> even frames
 *   Tier-3   every 4th, first at 15   -> frames = 3 (mod 4)
 *   Tier-4   every 8th, first at 65   -> frames = 1 (mod 8), so 1 (mod 4)
 *
 * which leaves Tier-4 the only slot Tier-2 and Tier-3 both leave free. Getting
 * there costs a two-frame start offset and nothing else. */
#define T4_START_FRAME        2
#define T4_FIRST_UPDATE_FRAME (T4_START_FRAME + T4_WIN_FRAMES - 1)

_Static_assert(T4_UPDATE_FRAMES % 4 == 0,
               "Tier-4's cadence is not a multiple of 4, so its updates do "
               "not keep a mod-4 slot and cannot be held off the other tiers");
_Static_assert(T4_FIRST_UPDATE_FRAME % 2 == 1,
               "Tier-4 updates on an EVEN frame, which is where a half-rate "
               "Tier-2 works");
_Static_assert(T4_FIRST_UPDATE_FRAME % 4 != T3_FIRST_UPDATE_FRAME % 4,
               "Tier-4 and Tier-3 update in the same mod-4 slot; the worst "
               "frame would carry both transforms");

/* How many frames the runtime probe watches before it reports. Starts after
 * the warm-up transitions so the mask it prints is the steady state, not the
 * priming. Tier-4 needs 65 frames before its first update, so the window must
 * outlast that or the probe reports a tier that has not started. */
#define SCHED_PROBE_FROM   72u
#define SCHED_PROBE_TO     264u

static float  *g_gwin[GUARD_N_CH];      /* per-channel sliding window       */
static cf32_t *g_gspec;                 /* [n_spec_ch][CFG_N_BINS]          */
static int16_t *g_gpend;                /* interleaved staging              */
static float  *g_gsum;                  /* summed window, SUMMED path only  */

/* ---- the per-gate instrument --------------------------------------------
 *
 * None of this gates anything. The per-gate counters say which gate throws a
 * real rig's frames away, on air rather than by inference from an offline
 * replay.
 *
 * `p` is the number that decides whether the chain can fire at all. Accept is
 * +1 and reject is -2 against a need of 6, so the drift per frame is 3p - 2
 * and the chain makes no progress unless p > 2/3. Near that boundary the
 * latency explodes: p = 0.75 fires in 0.77 s, p = 0.68 in 4.8 s, and p = 0.66
 * never fires at all.
 *
 * The denominator excludes `thr` and `jit`, for two different reasons.
 * A frame the score never lifted is not a frame a gate took away, so THR and
 * WARMUP are out. JIT is out because a jitter refusal is not a frame
 * rejection at all: that frame was ACCEPTED and counted in `acc`, and the
 * refusal happened later at fire time. Putting it in the denominator would
 * count the same frame on both sides. It is reported beside p instead. */
static nf_probe_t g_nfp;

/* One window's worth of gate accounting. THE SIX REASONS PARTITION THE FRAMES
 * EXACTLY - tracker_step writes exactly one DET_REJ_* per frame and the switch
 * below is exhaustive - so acc + thr + band + veto + nf + cont == frames, and
 * `TOT` is printed so that identity is visible rather than asserted.
 *
 * THR is a category, not a total: it counts frames whose score never cleared
 * the band threshold, plus the warmup frames. On a quiet window it dominates
 * every other category by an order of magnitude, which reads as missing
 * frames until the total is printed beside it. TOT removes the question. */
typedef struct {
    uint32_t acc, thr, band, veto, nf, cont, jit, frames, fast;
    /* The number that decides whether audio is actually lost. A frame over
     * the 32 ms hop is a warning: the DMA holds 96 ms of slack, three whole
     * hops, so an isolated 33.5 ms frame is handed back by the next 25 ms one.
     * Only a sustained mean over 32 ms loses audio, or a driver-reported
     * overflow, which source_i2s_quad counts. */
    uint64_t dt_sum_us;
    uint32_t dt_n;
} gate_counts_t;

static gate_counts_t g_gate;       /* accumulating, this window            */
static gate_counts_t g_gate_last;  /* the last COMPLETE window - displayed */
static gate_counts_t g_gate_fire;  /* snapshot at the deciding frame       */
static uint32_t      g_gate_win_ms;

/* ---- where the over-budget frames are, by which tier decided -------------
 *
 * A four-tier build measures several percent of frames over the 32 ms hop,
 * against a three-tier p99 of 29.30 ms with none over in n = 1938. It is a
 * real overrun rather than jitter: the frame timer starts after the I2S read
 * and the window fill, so it measures compute.
 *
 * The suspected mechanism is in detector_t4.c: t4_push_frame() accumulates
 * over T4_B_LO..T4_B_HI - 563 bins - on every frame, not only on the one frame
 * in eight where it decides. Its prominence slices are correctly scheduled
 * onto frames 1 (mod 4), disjoint from Tier-2's even frames, but the per-frame
 * accumulation is not scheduled at all, so it lands on the Tier-2 frames,
 * which are already the most expensive - worst v1 + T2 measured 33.5 ms.
 *
 * That is a hypothesis until these counters say so. `U c t4 0` and a rerun is
 * the decisive test, and this is the instrument that reads it: frames run and
 * frames over, split by which tier took a decision on them. If the overruns
 * are Tier-2 frames and they vanish with Tier-4 off, the mechanism is proved
 * and the fix is to schedule the accumulation. If they do not, it is not. */
#define OVER_BY_N 4      /* 0 = v1 alone, 1 = +T2, 2 = +T3, 3 = +T4 */
static uint32_t g_run_by[OVER_BY_N], g_over_by[OVER_BY_N];
static uint16_t g_sat_teeth, g_sat_gaps;         /* most recent frame      */
static uint16_t g_sat_teeth_fire, g_sat_gaps_fire;
static float    g_r1_fire, g_l_fire;
static uint32_t g_alerts_at_freeze;

/* One decimal with a sign, without %f: this image does not link newlib's
 * float formatting and every other number on these pages uses the same
 * integer trick (see CENT_I / CENT_F). */
static void fmt_db1(char *out, size_t n, float v)
{
    const bool neg = (v < 0.0f);
    float a = fabsf(v);
    if (!(a < 999.9f)) { a = 999.9f; }   /* also catches NaN, deliberately */
    const unsigned t = (unsigned)(a * 10.0f + 0.5f);
    snprintf(out, n, "%s%u.%u", neg ? "-" : "",
             (unsigned)((t / 10u) % 1000u), (unsigned)(t % 10u));
}

/* p as a PERCENTAGE of the frames that cleared the threshold, or -1 when none
 * did. A caller printing "0" for "no data" would report a dead detector.
 *
 * The denominator excludes thr and jit, for two different reasons. A frame the
 * score never lifted is not a frame a gate took away, so thr and warmup are
 * out. jit is out because a jitter refusal is not a frame rejection at all:
 * that frame was ACCEPTED and is already counted in acc, and the refusal came
 * later at fire time. Counting it here would count one frame on both sides. */
static int gate_p_pct(const gate_counts_t *g)
{
    const uint32_t den = g->acc + g->band + g->veto + g->nf + g->cont;
    if (den == 0u) {
        return -1;
    }
    return (int)((g->acc * 100u + den / 2u) / den);
}

/* FF as a PERCENTAGE of the window's frames with the floor on its FAST
 * constant. The room session asked whether FF was a count, a fraction or a
 * percentage; it is a percentage, and the page now says so with a %. */
static int gate_ff_pct(const gate_counts_t *g)
{
    if (g->frames == 0u) {
        return -1;
    }
    return (int)((g->fast * 100u + g->frames / 2u) / g->frames);
}

static void gate_count_frame(const frame_rec_t *rec)
{
    switch (rec->reject_reason) {
    case DET_REJ_NONE:   g_gate.acc++;  break;
    case DET_REJ_THR:
    case DET_REJ_WARMUP: g_gate.thr++;  break;
    case DET_REJ_BAND:   g_gate.band++; break;
    case DET_REJ_VETO:   g_gate.veto++; break;
    case DET_REJ_NF:     g_gate.nf++;   break;
    case DET_REJ_CONT:   g_gate.cont++; break;
    default: break;
    }
    g_gate.jit    += rec->jit_blocked ? 1u : 0u;
    g_gate.frames += 1u;
    g_gate.fast   += rec->floor_fast ? 1u : 0u;
    g_sat_teeth = rec->sat_teeth;
    g_sat_gaps  = rec->sat_gaps;
}

/* Close the window on a TIMER IN THE FRAME LOOP, not in test_publish().
 *
 * The room session's second defect: the reset used to live in test_publish(),
 * which runs ONLY while the TEST page is showing. With the page frozen on an
 * alert, or on MAIN, the counters accumulated unbounded - so `P .12` at
 * UP 00:27 described ten minutes of rig, music, chord and speech mixed
 * together and said nothing about any of them. Now the window is 5 s of wall
 * clock whatever the panel is doing. */
static void gate_window_tick(uint32_t now)
{
    if ((uint32_t)(now - g_gate_win_ms) >= TEST_REFRESH_MS) {
        g_gate_win_ms = now;
        g_gate_last = g_gate;
        memset(&g_gate, 0, sizeof(g_gate));
    }
}

/* ==========================================================================
 * The summed-window path.
 *
 * The guard used to run front_end - a Hann window and a 2048-point transform
 * - once per channel, and then sum the four spectra bin by bin. The DFT is
 * LINEAR and all four channels get the SAME window, so
 *
 *     sum_c FFT(w . x_c)  ==  FFT(w . sum_c x_c)
 *
 * exactly, in exact arithmetic. Summing the four windows first and
 * transforming once is the same combined spectrum for a quarter of the
 * transform cost - about 3.4 ms a frame of the quad build's 21.7, predicted
 * from a per-stage measurement of 0.84 ms of FFT plus 0.30 ms of magnitude
 * per channel.
 *
 * In float it is not bit-identical, and that is the only reason this is a
 * selectable path rather than a rewrite: four roundings of a sum of
 * transforms is not the same rounding as one transform of a sum. The claim
 * being made is decision identity, and it is a measurement - see
 * scripts/fft_path_proof.py, which replays archived four-channel device audio
 * through both paths and diffs above_thr / cont_accepted / chain / fired.
 *
 * What the path costs, stated plainly rather than buried:
 *
 *   - the per-channel spectra do not exist on it. A combiner_cx variant other
 *     than 'a' genuinely needs them, so the path is used only for 'a'.
 *   - Tier-2's kappa - the inter-capsule coherence it REPORTS but never
 *     decides on - cannot be computed. It reads NaN, which is the "not
 *     measured" value the host tools already skip, and never 1.0.
 *
 * It also gives memory back rather than taking it: the spectra block goes
 * from four channels to one, 32800 bytes to 8200, against 8192 for the summed
 * window. Net -16 KB on the path that fits three tiers.
 * ========================================================================== */
static int g_gspec_ch = GUARD_N_CH;

static void guard_free(void)
{
    for (int c = 0; c < GUARD_N_CH; c++) {
        free(g_gwin[c]);
        g_gwin[c] = NULL;
    }
    free(g_gspec);
    g_gspec = NULL;
    free(g_gpend);
    g_gpend = NULL;
    free(g_gsum);
    g_gsum = NULL;
}

static bool guard_alloc(bool summed)
{
    /* ~65 KB per-channel, ~49 KB summed, allocated per run and freed on exit
     * so the passive modes keep the heap they had. `I` reports the numbers. */
    for (int c = 0; c < GUARD_N_CH; c++) {
        g_gwin[c] = heap_caps_calloc(CFG_N_FFT, sizeof(float),
                                     MALLOC_CAP_INTERNAL | MALLOC_CAP_8BIT);
        if (!g_gwin[c]) {
            return false;
        }
    }
    g_gspec_ch = summed ? 1 : GUARD_N_CH;
    g_gspec = heap_caps_calloc((size_t)g_gspec_ch * CFG_N_BINS, sizeof(cf32_t),
                               MALLOC_CAP_INTERNAL | MALLOC_CAP_8BIT);
    g_gpend = heap_caps_calloc((size_t)CFG_HOP * GUARD_N_CH, sizeof(int16_t),
                               MALLOC_CAP_INTERNAL | MALLOC_CAP_8BIT);
    if (summed) {
        g_gsum = heap_caps_calloc(CFG_N_FFT, sizeof(float),
                                  MALLOC_CAP_INTERNAL | MALLOC_CAP_8BIT);
        if (!g_gsum) {
            return false;
        }
    }
    return g_gspec && g_gpend;
}

/* One quad frame loop, three modes:
 *   G  armed=true,  seconds=0, t2o=NULL -> runs until stopped, drives the
 *                                 actuators
 *   Z  armed=false, seconds=s, t2o=NULL -> bounded, ALSO streams the exact
 *                                 samples fed to the pipeline, so the host can
 *                                 re-run the Python reference on them and diff
 *                                 decisions
 *   H  armed=true,  t2o != NULL -> G, plus Tier-2 beside it and the alert
 *                                 driven by the OR of the two tiers
 * Sharing one loop is the same discipline as run_stream(): the acceptance test
 * must exercise the code the product actually runs, not a parallel copy.
 *
 * t2o == NULL IS TODAY'S BEHAVIOUR. Every Tier-2 line below is inside an
 * `if (t2o ...)`, so `G` and `Z` execute the instruction sequence they
 * executed before this build. That is what lets the golden gate keep meaning
 * what it meant. */
/* ---------------------------------------------------------------------------
 * The ambient bucket - a word for what the device is hearing.
 *
 * It is a QUANTISATION of the detector's own adaptive floor and adds no signal
 * processing: the floor is computed every frame regardless, and this reads its
 * mean once a second. Four words, with hysteresis, so it changes a handful of
 * times an hour rather than every frame - which is the only way a field on an
 * e-paper screen can carry it at all.
 *
 * The thresholds are provisional; see ui_config.h. The dB figure itself is
 * printed on the info page so they can be set from a real deployment rather
 * than from a guess.
 * ------------------------------------------------------------------------ */
static int ambient_db_now(void)
{
    if (!g_st || !g_st->have_floor) {
        return -99;
    }
    double acc = 0.0;
    for (int b = 0; b < CFG_N_BINS; b++) {
        acc += g_st->floor_[b];
    }
    const double mean = acc / (double)CFG_N_BINS;
    if (!(mean > 0.0)) {
        return -99;
    }
    return (int)(10.0 * log10(mean));
}

/* Hysteresis lives in the caller's state, not here: a bucket that recomputed
 * itself from scratch each second would flicker on every boundary. */
static const char *ambient_word(int db, uint8_t *bucket)
{
    static const char *W[4] = {"QUIET", "LOW", "BUSY", "LOUD"};
    const int edge[3] = {AMBIENT_DB_LOW, AMBIENT_DB_BUSY, AMBIENT_DB_LOUD};
    uint8_t b = *bucket;
    /* rise only past the edge, fall only past edge - hysteresis */
    while (b < 3 && db > edge[b] + AMBIENT_HYST_DB) {
        b++;
    }
    while (b > 0 && db < edge[b - 1] - AMBIENT_HYST_DB) {
        b--;
    }
    *bucket = b;
    return W[b];
}

/* x.xx from a float, without float printf: PicoLibC has none, which is why
 * the whole trace is binary. */
static int cent(float v)
{
    const float x = v * 100.0f + (v >= 0.0f ? 0.5f : -0.5f);
    if (x > 2000000.0f)  { return 2000000; }
    if (x < -2000000.0f) { return -2000000; }
    return (int)x;
}
#define CENT_I(v) (cent(v) / 100)
#define CENT_F(v) ((cent(v) < 0 ? -cent(v) : cent(v)) % 100)

/* ---- the deciding record ------------------------------------------------
 * One snapshot, taken at the frame whose comparison fired, read by the ALERT
 * screen, the ring, the LoRa packet, the test page and the console. Nothing
 * downstream is allowed a second opinion.
 *
 * Without it the ALERT screen reads a per-frame score, and the panel does not
 * draw until ALERT_SCREEN_START_MS after the decision - so the screen shows
 * the score from a frame well after the one that fired, and can display a
 * value below the threshold for an alert that was correct. The ring, written
 * in the same loop iteration as rec.fired, holds the right number, so the two
 * disagree. */
typedef struct {
    uint8_t  tier;          /* ALERT_TIER_*, NONE when nothing has fired   */
    uint8_t  fired_set;     /* EVLOG_FS_*, every tier that was up on this
                             * frame, not just the first in the priority
                             * order that `tier` reports                     */
    float    score;         /* the value the comparison used               */
    float    thr;           /* the constant it was compared against        */
    float    hz;            /* f0, or the rate for T3                      */
    uint32_t t_ms;
} decide_t;
static volatile decide_t g_decide;

/* The v1 threshold the detector is running, published from g_st->thr so every
 * surface that shows it reads one value. */
static volatile float g_run_thr1;

/* ---- the frozen alert page ----------------------------------------------
 * In test mode the panel stops being a live display at the instant of a
 * decision and becomes a record of it: every tier's score, threshold and f0 as
 * they were at that frame rather than as they are when the panel finally
 * draws, held until the operator taps.
 *
 * The point is a test run twenty metres away: the operator walks over when
 * they are ready and reads what the box heard, including what the tiers that
 * did not fire were doing at the same moment. That comparison is the
 * measurement, and a page that refreshed itself would destroy it. */
typedef struct {
    uint8_t  valid;
    uint8_t  tier;             /* the deciding tier, or ALERT_TIER_REMOTE   */
    uint16_t remote_id;
    uint16_t remote_thr1;
    float    remote_score;
    float    score[4];         /* v1, T2, T3, T4                            */
    float    thr[4];
    float    hz[4];            /* rate for T3                               */
    uint8_t  have[4];
    /* The instrument, at the deciding frame. R1 and L against rig distance
     * are what the near-field constants are set from, and a page that freezes
     * on the alert without carrying them loses the whole measurement. A page
     * that holds the deciding frame must hold all of it. */
    float    r1_db, l_db, r_db;
    uint16_t sat_t, sat_g;
    int16_t  p_pct, ff_pct;       /* -1 when the window had no data          */
    uint32_t g_acc, g_thr, g_band, g_veto, g_nf, g_cont, g_jit, g_tot;
    uint32_t alerts_at_freeze;    /* so a later reader can tell if more came */
} frozen_t;
static volatile frozen_t g_frozen;

typedef struct {
    float    v1_score, v1_thr, v1_hz;
    float    t2_score, t2_thr, t2_hz;
    float    t3_score, t3_thr, t3_rate;
    float    t4_score, t4_thr, t4_hz;
    /* One running maximum per tier: four comparisons per frame, and nothing
     * else in the frame loop moves. The instantaneous score alone is useless
     * during a test, because the repaint is every few seconds and a tier's
     * score can peak and fall back between two of them - "nothing happened"
     * and "T2 reached 0.91 of 1.15" would look identical. The UI clears these
     * when it reads them, so each repaint reports the window since the
     * previous one.
     *
     * Read and cleared from the UI task while the frame loop writes them. A
     * torn read costs at worst one frame's peak on one repaint, which is why
     * no lock is taken: locking the frame loop to protect a display number
     * would be a real cost paid for a cosmetic one. */
    float    v1_pk, t2_pk, t3_pk, t4_pk;
    /* When each tier last wrote a record. The frozen page needs a number for
     * every tier at the deciding frame, and a tier that updates one frame in
     * eight has no fresh score on most frames. With this, "no candidate right
     * now" prints the last score it did have instead of a word. */
    uint32_t seen_ms[4];
    uint8_t  have2, have3, have4;
} info_snap_t;
static volatile info_snap_t g_info;

/* Frames whose measured cost exceeded the hop, since power-on. The number to
 * watch when the frame budget is thin. */
static volatile uint32_t g_frames_over;
static uint32_t s_info_last_ms;
/* Test mode's own repaint clock and near-miss tally. Declared here rather
 * than beside test_publish() because the frame loop above reads them and a
 * file-scope static cannot be forward declared. */
static uint32_t s_test_last_ms;
static uint32_t s_near_count;
/* The frozen page is drawn once per freeze, not once per frame. */
static bool s_frozen_drawn;
/* The alert tier on the previous frame, so the freeze can be taken on the
 * onset edge for every alert path. */
static uint8_t s_prev_alert_tier;
/* The link test's last outcome, for the TEST page. */
static volatile uint8_t  g_link_state;

/* ---- `Lp <N>`: ping every N seconds -------------------------------------
 * A range walk needs the box to keep asking while the operator carries the
 * other unit away, since a single `Ls` is useless once you are 50 m from the
 * keyboard. This reuses the existing link-test packet rather than adding a
 * second message to the air interface: detection and local alerting only, and
 * the radio carries one message. */
static volatile uint32_t g_ping_period_s;   /* 0 = off                      */
static volatile uint32_t g_ping_due_ms;
static volatile uint32_t g_ping_tx, g_ping_rx;
static volatile uint16_t g_link_peer;
static volatile uint32_t g_link_ms;

static int run_quad_pipeline(uint32_t seconds, bool armed, double thr,
                             const guard_t2_opts_t *t2o,
                             const guard_t3_opts_t *t3o,
                             const guard_t4_opts_t *t4o, bool standalone)
{
    const bool t2on = (t2o != NULL && t2o->enable);
    const bool t3on = (t3o != NULL && t3o->enable);
    /* The near-field gate, declared here beside t2on/t3on for the same reason
     * loraon, poweron and disp_on are: the no-regression certificate audits
     * this function for code the untouched modes would execute, and "the
     * sealed path is unchanged" has to be readable at the line rather than
     * derived from a settings call three files away. */
    const bool nfon = (settings_get()->nf_gate != 0);
    const bool t4on = (t4o != NULL && t4o->enable);
    /* THE RADIO IS LIVE IN THE FIELD MODE ONLY.
     *
     * `G`, `Z`, `H` and every bounded capture are LAB runs, judged on
     * decision-for-decision identity, and a lab session that started
     * transmitting - or that answered a colleague's bench test with a buzzer -
     * would be a surprise nobody asked for. The standalone guard is the mode
     * where "everyone alerts everyone" is the design; it is also the only
     * mode that calls lora_link_begin(). So this is `standalone` and the
     * radio actually answering, and on a board with no radio it is a compiled
     * zero. */
    const bool lora_on = standalone && armed && lora_link_ready();
    /* Same discipline for the battery bar. On the breadboard this is a
     * compiled zero and the operator surface is byte-for-byte what it was; on
     * the PCB it is what puts the bar on the LISTENING screen. Declared here
     * beside the tier flags so the certificate's mode-isolation audit can see
     * the guard - and so a reader of the frame loop can too. */
    const bool power_on = armed && (BOARD_HAS_VBAT != 0);
    /* THE OPERATOR DISPLAY runs on an armed guard and nowhere else. `Z` - the
     * unarmed capture path through this same function - must execute none of
     * it, and naming the condition here is what lets certify.py's mode
     * isolation audit say so at the line rather than derive it from a call
     * graph. Same arrangement as lora_on and power_on above. */
    const bool disp_on = armed;
    /* The summed-window path is used whenever nothing downstream needs the
     * per-channel spectra: that is every combiner but the experimental ones.
     * Selected here, printed at arming, never guessed at by the frame loop. */
    const bool summed = !t2on || t2o->cx == 'a';
    const char cmd = t2on ? 'H' : (armed ? 'G' : 'Z');
    const char cmds[2] = {cmd, '\0'};

    /* The mono modes' 12 KB is not needed while the guard runs, and with
     * three tiers it is the difference between fitting and not. */
    mono_free();

    /* ---- allocation order, and the claimant that is not here ------------
     * The per-run set is I2S (48 KB of DMA) + guard (70 KB) + Tier-2 (24 KB),
     * in this order. Tier-3's 13 KB is deliberately not in it; see
     * t3_boot_alloc().
     *
     * The order is load-bearing and took three measurements to settle. With
     * Tier-3 allocating per-run, I2S first left it without a contiguous 12688
     * (18616 free, largest 7680), and I2S last left the SECOND bus without its
     * 24576 (57180 free, largest 31744). A reservation - take the DMA's 48 KB
     * as one block, hand it back just before the driver asks - moved the
     * failure onto the guard's 32800-byte spectra instead. The heap has no
     * placement that fits four large claimants; the answer was to stop having
     * four, not to shuffle them. */
    const char *stage = NULL;
    if (!guard_alloc(summed)) {
        stage = summed ? "guard buffers (~54 KB, summed-window path)"
                       : "guard buffers (70 KB, incl. one 32800-byte spectra "
                         "block)";
    } else if (source_i2s_quad_start() != ESP_OK) {
        stage = "the I2S buses (48 KB of DMA)";
    } else if (t2on && !t2_alloc(t2o->cx != 'a')) {
        stage = "Tier-2 state (24 KB)";
    } else if (t4on && !t4_alloc()) {
        stage = "Tier-4 state (~10 KB)";
    } else if (t3on && !t3_alloc()) {
        stage = "Tier-3 state - it is claimed at BOOT, so this means boot "
                "could not get it";
    }
    /* NAME THE STAGE THAT FAILED, and print the heap. The old message said
     * "out of RAM" whatever went wrong, including a Tier-3 FFT init that had
     * not allocated anything at all - a message that sends the next session
     * looking in the wrong place, and did. */
    if (stage) {
        char b[128];
        snprintf(b, sizeof(b), "ERR quad: could not start - %s\n", stage);
        trace_text(b);
        heap_line("at failure");
        source_i2s_quad_stop();
        t3_free();
        t2_free();
        guard_free();
        trace_ack(cmds, TRACE_ACK_FAULT);
        return RUN_END_COMPLETE;
    }
    {
        char pb[160];
        snprintf(pb, sizeof(pb),
                 "FFT path: %s (%d transform%s/frame)%s\n",
                 summed ? "summed window" : "per channel",
                 summed ? 1 : GUARD_N_CH, summed ? "" : "s",
                 summed ? ", kappa not measured" : "");
        trace_text(pb);
    }
    heap_line("armed");

    if (armed) {
        /* The panel is alert_ui's from here: its first tick asks for
         * LISTENING. Requesting it here as well cost a second full refresh -
         * four seconds of a panel that is 2 s per update - for no extra
         * information. */
        alert_ui_begin(cmd);
    }

    trace_hdr_t h = {
        .magic = TRACE_MAGIC_HDR, .version = TRACE_VERSION,
        .n_frames = 0,
        .n_samples = seconds * CFG_FS,
        .threshold = thr,
        .fs = CFG_FS, .n_fft = CFG_N_FFT, .hop = CFG_HOP,
        .n_bins = CFG_N_BINS, .n_f0 = CFG_N_F0,
        .rec_size = sizeof(trace_rec_t),
    };
    strncpy(h.name, t2on ? "guard_quad_t2"
                         : (armed ? "guard_quad" : "quad_parity"),
            sizeof(h.name) - 1);
    /* NO HEADER FOR A STANDALONE RUN - the same reasoning that withholds the
     * sentinel, and it took a failed golden gate to notice the other half.
     *
     * With autostart on and a header emitted, a later bounded capture reads
     * back the guard's header instead of its own - the frames are the
     * replay's, the header is whatever was still in the link when the host
     * connected - and the golden comparison fails on a device whose detector
     * is perfectly correct.
     *
     * HDR and END are framing for a bounded capture. A standalone guard is not
     * one: it is unbounded, nobody is necessarily reading it, and the same
     * information is in the plain-text banner above, which every parser skips
     * by design. Emitting neither is what makes autostart safe to leave on. */
    if (!standalone) {
        trace_send_hdr(&h);
    }

    detector_state_reset(g_st, thr);
    /* THE FAMILY RULE, from the persisted settings and DEFAULT OFF. Set after
     * the reset because the reset memsets - which is also what guarantees a
     * run that does not ask for it gets the sealed tracker. It applies to
     * every armed mode including `G`, deliberately: a variant that could only
     * be exercised in the field mode could not be characterised on the bench.
     * The flag is what the trace and the banner report. */
    g_st->trk_family = (settings_get()->trk_family != 0);
    if (g_st->trk_family) {
        trace_text("TRK family {2,3} continuity ON (normalised jitter) - "
                   "adopt-ELIGIBLE, not the shipped default\n");
    }
    /* THE VETO, same discipline: the flag is what the trace and the banner
     * report, so a run is always self-describing about which detector it was.
     * A device that fires on a piano and a device that does not are different
     * instruments, and a log that does not say which one produced it cannot
     * be used to judge either. */
    g_st->veto_voice = (settings_get()->veto_voice != 0);
    if (g_st->veto_voice) {
        char bv[128];
        snprintf(bv, sizeof(bv),
                 "VETO voice/struck-note ON: f0 >= %.0f Hz AND teeth >= %d\n",
                 (double)CFG_VETO_F0_MIN_HZ, (int)CFG_VETO_MIN_TEETH);
        trace_text(bv);
    }
    /* Printed for the same reason the veto line is: the settings line says
     * what is stored and this says what the detector took, and the difference
     * between those two claims can be a device that sees nothing. */
    g_st->nf_gate = nfon;
    {
        char bn[160];
        if (nfon) {
            snprintf(bn, sizeof(bn),
                     "NF near-field gate ON: jitter <= %.3f, and at score >= "
                     "%.2f require R >= %.1f dB\n",
                     (double)CFG_MAX_JITTER_FIELD, (double)CFG_NF_SCORE_HI,
                     (double)CFG_NF_R_MIN_DB);
        } else {
            snprintf(bn, sizeof(bn),
                     "NF near-field gate OFF: sealed jitter <= %.3f, no R "
                     "requirement (sealed behaviour)\n",
                     (double)CFG_MAX_JITTER);
        }
        trace_text(bn);
    }
    /* ---- test mode is announced, loudly ---------------------------------
     * It changes the glass, the ring, the radio payload and the console and
     * nothing about detection, so a unit in test mode detects exactly as a
     * unit out of it. That is precisely why it has to be printed: a posture
     * that is invisible in the numbers is a posture somebody will carry to a
     * deployment. The home screen carries the same tag for the operator who
     * has no laptop. */
    if (settings_get()->test_mode) {
        trace_text("TEST MODE: bench posture. Detection, thresholds, alert "
                   "timing and outputs are UNCHANGED.\n");
    }
    /* ---- the four compiled thresholds, on one line ----------------------
     * Each tier also prints its own further down, which means answering "what
     * is this image's operating point" from those alone requires reading four
     * separate lines and knowing that the v1 one is in milli-units and the
     * rest are not. Together and in the same units, a session log can be
     * checked at a glance. */
    {
        char bt[192];
        /* ---- the running v1, read from what the detector compares -------
         * g_st->thr is not a copy of the threshold, it is the threshold:
         * detector_state_reset() assigns it and detector.c compares
         * `score > band_threshold(f0, st->thr)` against it. Printing
         * a settings field or the compiled constant here would be printing
         * something that OUGHT to equal what the detector uses, and this
         * banner exists precisely because those two drifted apart once
         * already.
         *
         * The compiled default appears only when it differs, so the ordinary
         * board prints one number and the paired board prints the difference
         * it was configured for. */
        const double run_v1 = g_st->thr;
        /* PUBLISHED ONCE so the TEST page header, the frozen page and this
         * banner cannot re-derive it differently. Re-deriving a displayed
         * number from its source constants is exactly what put 1.65 on an
         * ALERT screen. */
        g_run_thr1 = (float)run_v1;
        char v1s[48];
        if (fabs(run_v1 - (double)DEFAULT_THRESHOLD) < 1e-9) {
            snprintf(v1s, sizeof(v1s), "v1=%.4f", run_v1);
        } else {
            snprintf(v1s, sizeof(v1s), "v1=%.4f (compiled %.4f)",
                     run_v1, (double)DEFAULT_THRESHOLD);
        }
        snprintf(bt, sizeof(bt),
                 "THRESHOLDS running %s  t2=%.4f  t3=%.4f  t4=%.4f\n",
                 v1s, (double)T2_TAU2, (double)T3_TAU3, (double)T4_TAU4);
        trace_text(bt);
        /* ---- the unit and its one variable ------------------------------
         * A paired field configuration differs by v1's threshold and nothing
         * else, so every disagreement between the two boards has exactly one
         * possible cause. That is only legible if each board says which one
         * it is, and the running threshold is the settings value rather than
         * the compiled default. */
        const uint32_t t1 = settings_get()->thr1_milli
                                ? settings_get()->thr1_milli
                                : (uint32_t)(DEFAULT_THRESHOLD * 1000.0 + 0.5);
        snprintf(bt, sizeof(bt), "UNIT N-%04X thr %lu.%02lu\n",
                 (unsigned)lora_link_device_id(),
                 (unsigned long)(t1 / 1000u),
                 (unsigned long)((t1 % 1000u) / 10u));
        trace_text(bt);
    }
    if (t4on) {
        t4_reset(g_t4st);
        char b4[160];
        snprintf(b4, sizeof(b4),
                 "T4 tau4_milli=%d grid=%d-%dHz nharm=%d n4=%d m4=%d "
                 "upd=%d frames warmup_ms=%d\n",
                 (int)(t4o->cfg.tau4 * 1000.0 + 0.5),
                 (int)T4_F0_LO, (int)T4_F0_HI, T4_N_HARM,
                 t4o->cfg.n4, t4o->cfg.m4, T4_UPDATE_FRAMES,
                 (int)(t4o->cfg.warmup_s * 1000.0));
        trace_text(b4);
    }
    if (t3on) {
        t3_reset(g_t3st);
        char b[128];
        snprintf(b, sizeof(b),
                 "T3 tau3_milli=%d fire=%d-%dHz n3=%d m3=%d nharm=%d "
                 "warmup_ms=%d\n",
                 (int)(t3o->cfg.tau3 * 1000.0 + 0.5),
                 (int)t3o->cfg.fire_lo, (int)t3o->cfg.fire_hi,
                 t3o->cfg.n3, t3o->cfg.m3, t3o->cfg.n_harm,
                 (int)(t3o->cfg.warmup_s * 1000.0));
        trace_text(b);
    }
    if (t2on) {
        t2_state_reset(g_t2st);
        /* Integers only: PicoLibC's printf has no float support, which is why
         * the whole trace is binary. tau2 and busoff go out in MILLI-units,
         * the same units the `H` command takes them in. */
        char b[128];
        snprintf(b, sizeof(b),
                 "T2 tau2_milli=%d N2=%d M2=%d gap=%d rel=%d rate=%s cx=%c "
                 "busoff_milli=%d\n",
                 (int)(t2o->cfg.tau2 * 1000.0 + 0.5), t2o->cfg.n2,
                 t2o->cfg.m2, t2o->cfg.gap, t2o->cfg.release,
                 t2o->cfg.decim == 2 ? "half" : "full", t2o->cx,
                 (int)(t2o->busoff * 1000.0f));
        trace_text(b);
    }

    /* From here to the end of the loop the audio path is HOT: nothing may
     * block on the panel. epaper_wait_idle() enforces it. */
    epaper_set_audio_hot(true);

    uint32_t frame = 0;
    uint32_t pcm_seq = 0, sample_index = 0;
    const uint32_t n_total = seconds * CFG_FS;
    bool stop_after_this = false;
    uint32_t pend = 0;              /* frames waiting in g_gpend            */
    uint32_t filled = 0;            /* samples of window primed so far      */
    uint8_t prev_fired = 0;
    uint8_t prev_fired2 = 0;
    uint8_t prev_fired3 = 0;
    uint8_t prev_fired4 = 0;
    bool    alert_open = false;     /* the OR, for the event ring           */
    /* Sentinel telemetry, so the quad END record says what the mono one says.
     * The quad parity gate compares the device's sentinel against the
     * reference's own longest_chain and n_floor_fast; leave them unfilled and
     * that gate reports FAIL with zero decision mismatches on every run it
     * ever does. A gate that fails for a reason unrelated to what it gates is
     * worse than no gate. These are counters over records that already exist;
     * no decision reads them. */
    /* THE FOOTER'S TWO FACTS, sampled once a second.
     *
     * "are all four microphones alive" and "which algorithms are running" are
     * the two questions a field session keeps asking, and until now both
     * needed a laptop. The RMS is taken from the newest hop of the windows
     * front_end has already been handed - no new buffer, no new read - and
     * only on every 32nd frame, so the cost is ~0.3 us/frame amortised against
     * the 1.1 ms of headroom the guard has left. epaper_set_footer() is a
     * strncpy; it never draws and never blocks. */
    uint32_t foot_next = 0;
    /* THE OPERATOR DISPLAY's own state, held across the run: the snapshot
     * being maintained, and which hour its time fields were last refreshed
     * on. Zero-initialised, so the first second of a run publishes once and
     * then goes quiet until something happens. */
    epaper_main_t disp = {0};
    uint32_t disp_hour = 0xFFFFFFFFu;
    /* The ambient bucket's hysteresis state, and the raw dB behind it. The
     * info page prints the number so the thresholds can be set from a real
     * deployment rather than from ui_config.h's provisional values. */
    uint8_t  amb_bucket = 0;
    int      amb_db = -99;
    float   peak_score = -1e30f;
    int32_t longest_chain = 0;
    uint32_t n_floor_fast = 0;
    float   last_score2 = 0.0f;     /* Tier-2's score on its last step      */
    float   last_W = 0.0f;          /* Tier-3's W on its last update        */
    float   last_W4 = 0.0f;         /* Tier-4's W4 on its last update       */
    int64_t t3_us_prev = 0;         /* us_front+us_score are RUNNING TOTALS */
    int     end_reason = RUN_END_COMPLETE;
    uint32_t empty = 0;
    bool alerted_once = false;

    /* The scheduling probe: two 4-bit masks saying which frame slots each
     * tier made expensive, and the worst frame time seen in each class,
     * reported once. Measured rather than assumed, because the tier phases are
     * arithmetic that a comment cannot enforce. Four ops a frame for 128
     * frames, then nothing. */
    uint8_t  sched_t2 = 0, sched_t3 = 0, sched_t4 = 0;
    uint32_t worst_plain = 0, worst_t2 = 0, worst_t3 = 0, worst_both = 0;
    bool     sched_done = false;

    for (;;) {
        const int n = source_i2s_quad_read(g_quad);
        if (n <= 0) {
            /* A bus stopped. Say so loudly and keep trying: going quiet here
             * is the failure mode that wastes a whole session. */
            if (++empty % 8u == 1u) {
                trace_stat_t s = {0};
                s.magic = TRACE_MAGIC_STA;
                s.mode = 'G';
                s.uptime_ms = now_ms();
                s.button_level = 1;
                trace_send_stat(&s);
            }
            if (armed) {
                /* SAY IT ON THE BOX. A standalone device has no console to
                 * print STAT records to, and "the panel still says LISTENING
                 * while no audio has arrived for a minute" is the failure
                 * that comes home with an empty capture. */
                alert_ui_fault_led(now_ms());
            }
            if (run_should_stop(standalone, armed, &end_reason)) {
                break;
            }
            continue;
        }
        empty = 0;

        /* PARITY: emit the samples BEFORE the frames derived from them, in
         * contiguous sequence-numbered blocks, so the host reconstructs
         * exactly the array the pipeline consumed. */
        if (!armed) {
            trace_send_pcm4(pcm_seq++, sample_index, g_quad,
                            (uint16_t)n, QUAD_N_CH);
            sample_index += (uint32_t)n;
            if (n_total && sample_index >= n_total) {
                stop_after_this = true;
            }
        }

        for (int f = 0; f < n; f++) {
            for (int c = 0; c < GUARD_N_CH; c++) {
                g_gpend[pend * GUARD_N_CH + c] = g_quad[f * GUARD_N_CH + c];
            }
            pend++;
            if (pend < CFG_HOP) {
                continue;
            }
            pend = 0;

            /* slide every channel's window by one hop, append the new block */
            for (int c = 0; c < GUARD_N_CH; c++) {
                memmove(g_gwin[c], g_gwin[c] + CFG_HOP,
                        (CFG_N_FFT - CFG_HOP) * sizeof(float));
                float *dst = g_gwin[c] + (CFG_N_FFT - CFG_HOP);
                for (int k = 0; k < CFG_HOP; k++) {
                    dst[k] = q_to_f(g_gpend[k * GUARD_N_CH + c]);
                }
            }
            /* R1 and L, from channel 0 only.
             *
             * Fed here rather than after the priming check so the biquads see
             * a continuous sample stream: a filter that skips the first three
             * hops carries their transient into the first frame anybody
             * reads. The 30 s reference settles during priming for the same
             * reason. See nf_probe.h for why one channel and not the sum. */
            nf_probe_frame(&g_nfp, g_gwin[0] + (CFG_N_FFT - CFG_HOP), CFG_HOP);
            if (filled < CFG_N_FFT) {
                filled += CFG_HOP;
                if (filled < CFG_N_FFT) {
                    continue;          /* window not primed yet */
                }
            }

            const double t = (double)((double)frame * CFG_HOP + CFG_N_FFT) /
                             (double)CFG_FS;
            frame_rec_t rec;
            const int64_t c0 = esp_timer_get_time();
            const cf32_t *sp;
            if (summed) {
                /* ONE transform. The sum is the combined spectrum already, so
                 * there is no combiner call left to make - which is also why
                 * this cannot silently diverge from combiner(): it is not a
                 * second implementation of it, it is the same arithmetic done
                 * before the transform instead of after. */
                for (int i = 0; i < CFG_N_FFT; i++) {
                    float a = g_gwin[0][i];
                    for (int c = 1; c < GUARD_N_CH; c++) {
                        a += g_gwin[c][i];
                    }
                    g_gsum[i] = a;
                }
                front_end(g_gsum, g_gspec, g_w);
                sp = g_gspec;
            } else {
                for (int c = 0; c < GUARD_N_CH; c++) {
                    front_end(g_gwin[c], &g_gspec[(size_t)c * CFG_N_BINS],
                              g_w);
                }
                /* `G`/`Z` call the sealed combiner directly. `H` with cx 'a' -
                 * the default - reaches the SAME function through combiner_cx,
                 * which returns combiner()'s own result rather than a
                 * reimplementation of it. */
                sp = t2on
                    ? combiner_cx(t2o->cx, t2o->f_split_hz, t2o->busoff,
                                  g_gspec, GUARD_N_CH, g_w, g_cxw)
                    : combiner(g_gspec, GUARD_N_CH, g_w);
            }
            back_end(sp, g_st, t, frame, g_w, &rec);
            t2_rec_t t2r;
            bool t2ran = false;
            if (t2on) {
                t2ran = t2_step(sp, summed ? NULL : g_gspec, GUARD_N_CH,
                                &t2o->cfg, g_t2st, t, frame, g_t2w, &t2r);
            }
            /* ---- TIER-3, on the RAW BLOCK ------------------------------
             * A different seam from Tier-2 on purpose: a per-frame band energy
             * is sampled at 31.25 Hz, whose Nyquist is 15.6 Hz, so it cannot
             * see an 82 Hz modulation. Tier-3 therefore takes the newest hop
             * of each channel's window - the same samples front_end just
             * consumed, before the window and the transform.
             *
             * The first frame used to be skipped, and the skip was backwards.
             * The comment that stood here said the skip moved Tier-3's updates
             * onto odd frames so they never landed on Tier-2's even ones. The
             * arithmetic says the opposite, and it is arithmetic, not opinion
             * - see T3_FIRST_UPDATE_FRAME above. Tier-3 needs T3_ENV_NFFT
             * envelope samples before its FIRST transform, which is 16 pushes,
             * so the first transform lands on the SIXTEENTH frame it sees, not
             * the first. Starting at frame 0 puts it on frame 15 - odd, and
             * disjoint from Tier-2. Starting at frame 1 put it on frame 16 -
             * EVEN, landing on Tier-2's step on every single update.
             *
             * It never showed up because it cannot: the pair builds have only
             * ever run one of the two tiers, and one tier cannot collide with
             * a tier that is not there. It would have shown up on the first
             * all-three frame as roughly 21.7 + 7.5 + 9.1 = 38 ms against a
             * 32 ms hop. The probe below MEASURES the two cadences rather than
             * trusting either comment. */
            t3_rec_t t3r;
            bool t3ran = false;
            if (t3on) {
                const float *chp[GUARD_N_CH];
                for (int c = 0; c < GUARD_N_CH; c++) {
                    chp[c] = g_gwin[c] + (CFG_N_FFT - CFG_HOP);
                }
                t3ran = t3_push_block(chp, GUARD_N_CH, &t3o->cfg, g_t3st,
                                      armed && alert_ui_outputs_active(),
                                      &t3r);
            }
            /* ---- TIER-4, on the COMBINED SPECTRUM ----------------------
             * The cheapest seam of the four: it consumes the array back_end
             * was just handed, so it costs no transform. The two-frame start
             * offset is the whole of its scheduling - see T4_START_FRAME. */
            t4_rec_t t4r;
            bool t4ran = false;
            if (t4on && frame >= T4_START_FRAME) {
                t4ran = t4_push_frame(sp, &t4o->cfg, g_t4st,
                                      (uint32_t)frame, t,
                                      armed && alert_ui_outputs_active(),
                                      &t4r);
                if (t4ran) {
                    /* THIS WAS MISSING AND THE PANEL SAID "T4 OFF" FOREVER.
                     * have2 and have3 are set at their own tiers, and have4
                     * has to be set here or the info page reads "T4 OFF" on a
                     * board that is running Tier-4 the whole time - the worst
                     * kind of display bug, because the only way to catch it is
                     * to disbelieve the device. */
                    g_info.t4_score = (float)t4r.W4;
                    if ((float)t4r.W4 > g_info.t4_pk) { g_info.t4_pk = (float)t4r.W4; }
                    g_info.t4_hz    = (float)t4r.f0;
                    g_info.t4_thr   = (float)t4o->cfg.tau4;
                    g_info.have4    = 1u;
                    g_info.seen_ms[3] = now_ms();
                }
            }
            const uint32_t dt = (uint32_t)(esp_timer_get_time() - c0);
            /* THE DROP ACCOUNTING. One hop is 32 ms; a frame that took longer
             * than that did not merely run late, it means audio was dropped,
             * which is the one failure this device cannot have during an
             * alert. Counted here because this is the only place the measured
             * cost of a frame exists. */
            {
                /* SCHED proves at most one tier decides on a frame, so this
                 * classification is a partition. Tier-4's per-frame
                 * accumulation is in EVERY bucket, which is the point. */
                const int ob = t2ran ? 1 : (t3ran ? 2 : (t4ran ? 3 : 0));
                if (g_run_by[ob] < 0xFFFFFFFFu) { g_run_by[ob]++; }
                if (dt > 32000u && g_over_by[ob] < 0xFFFFFFFFu) {
                    g_over_by[ob]++;
                }
            }
            g_gate.dt_sum_us += dt;
            g_gate.dt_n++;
            if (dt > 32000u) {
                if (g_frames_over < 0xFFFFFFFFu) {
                    g_frames_over++;
                }
                bootrec_count_drop();
            }
            gate_count_frame(&rec);
            gate_window_tick(now_ms());
            g_info.v1_score = (float)rec.score;
            if ((float)rec.score > g_info.v1_pk) { g_info.v1_pk = (float)rec.score; }
            g_info.v1_hz    = (float)rec.f0_hz;
            g_info.v1_thr   = (float)thr;
            g_info.seen_ms[0] = now_ms();

            if (!sched_done && frame >= SCHED_PROBE_FROM) {
                const uint8_t slot = (uint8_t)(1u << (frame & 3u));
                if (t2ran) { sched_t2 |= slot; }
                if (t3ran) { sched_t3 |= slot; }
                if (t4ran) { sched_t4 |= slot; }
                uint32_t *w = t2ran ? (t3ran ? &worst_both : &worst_t2)
                                    : (t3ran ? &worst_t3   : &worst_plain);
                if (dt > *w) { *w = dt; }
                if (frame >= SCHED_PROBE_TO) {
                    char sb[224];
                    const bool clash = (sched_t2 & sched_t3) ||
                                       (sched_t2 & sched_t4) ||
                                       (sched_t3 & sched_t4);
                    snprintf(sb, sizeof(sb),
                             "SCHED t2=%X t3=%X t4=%X mod4 %s  "
                             "worst us: v1 %u, +t2 %u, +t3 %u, both %u\n",
                             (unsigned)sched_t2, (unsigned)sched_t3,
                             (unsigned)sched_t4,
                             clash ? "COLLIDE" : "disjoint",
                             (unsigned)worst_plain, (unsigned)worst_t2,
                             (unsigned)worst_t3, (unsigned)worst_both);
                    trace_text(sb);
                    /* Say it twice when it is wrong. A standalone box has no
                     * console, and this is the line that explains a p99 over
                     * the hop before anyone starts bisecting the detector. */
                    if (clash) {
                        trace_text("BUG two tiers are working on the same "
                                   "frames; the worst frame carries both. "
                                   "See T3_FIRST_UPDATE_FRAME and "
                                   "T4_START_FRAME.\n");
                    }
                    sched_done = true;
                }
            }

            trace_rec_t r = {
                .magic = TRACE_MAGIC_REC,
                .frame = rec.frame, .t_s = rec.t_s, .score = rec.score,
                .f0_bin = rec.f0_bin, .f0_hz = rec.f0_hz,
                .f0_raw_hz = rec.f0_raw_hz, .teeth = rec.teeth,
                .floor_fast = rec.floor_fast, .reanch = rec.reanch,
                .n_held_bins = rec.n_held_bins, .above_thr = rec.above_thr,
                .cont_accepted = rec.cont_accepted, .chain = rec.chain,
                .fired = rec.fired, .is_octave = rec.is_octave,
                .us_frame = dt,
            };
            trace_send_rec(&r);
            if (rec.score > peak_score) {
                peak_score = rec.score;
            }
            if ((int32_t)rec.chain > longest_chain) {
                longest_chain = (int32_t)rec.chain;
            }
            n_floor_fast += rec.floor_fast ? 1u : 0u;

            if (rec.fired && !prev_fired) {
                trace_alt_t a = {.magic = TRACE_MAGIC_ALT, .frame = frame,
                                 .t_s = t, .f0_hz = rec.f0_hz,
                                 .score = rec.score, .chain = rec.chain,
                                 .n_events = (uint32_t)g_st->n_events + 1u};
                trace_send_alt(&a);
                alerted_once = true;
            }
            prev_fired = rec.fired;

            if (t2ran) {
                trace_t2r_t tr = {
                    .magic = TRACE_MAGIC_T2R, .frame = t2r.frame,
                    .t_s = t2r.t_s, .score2 = t2r.score2,
                    .f02_hz = t2r.f02_hz, .f02_row = t2r.f02_row,
                    .teeth2 = t2r.teeth2, .hit = t2r.hit,
                    .fired2 = t2r.fired2, .excluded = t2r.excluded,
                    .hits = t2r.hits, .n2 = t2r.n2,
                    .track_age = t2r.track_age, .kappa = t2r.kappa,
                    .us_t2 = t2r.us_t2};
                trace_send_t2r(&tr);
                last_score2 = t2r.score2;
                g_info.t2_score = (float)t2r.score2;
                if ((float)t2r.score2 > g_info.t2_pk) { g_info.t2_pk = (float)t2r.score2; }
                g_info.t2_hz    = (float)t2r.f02_hz;
                g_info.t2_thr   = (float)t2o->cfg.tau2;
                g_info.have2    = 1u;
                    g_info.seen_ms[1] = now_ms();
                if (t2r.fired2 && !prev_fired2) {
                    trace_al2_t a2 = {
                        .magic = TRACE_MAGIC_AL2, .frame = frame, .t_s = t,
                        .f02_hz = g_t2st->f0_on, .score2 = t2r.score2,
                        .hits = t2r.hits, .kappa = t2r.kappa,
                        .n_events = (uint32_t)g_t2st->n_events + 1u};
                    trace_send_al2(&a2);
                    alerted_once = true;
                }
                prev_fired2 = t2r.fired2;
            }

            if (t3ran) {
                const int64_t t3_us_now = g_t3st->us_front + g_t3st->us_score;
                const uint32_t t3_us = (uint32_t)(t3_us_now - t3_us_prev);
                t3_us_prev = t3_us_now;
                trace_t3r_t t3rec = {
                    .magic = TRACE_MAGIC_T3R, .frame = frame,
                    .t_s = t3r.t, .r_hz = t3r.r, .W = t3r.W,
                    .r_any_hz = t3r.r_any, .W_any = t3r.W_any,
                    .hits = t3r.hits, .n3 = t3r.n3,
                    .track_age = t3r.track_age,
                    .hit = t3r.hit ? 1u : 0u,
                    .fired3 = t3r.fired3 ? 1u : 0u,
                    .frozen = t3r.frozen ? 1u : 0u, .pad = 0u,
                    .us_t3 = t3_us};
                trace_send_t3r(&t3rec);
                last_W = (float)t3r.W;
                g_info.t3_score = (float)t3r.W;
                if ((float)t3r.W > g_info.t3_pk) { g_info.t3_pk = (float)t3r.W; }
                g_info.t3_rate  = (float)t3r.r;
                g_info.t3_thr   = (float)t3o->cfg.tau3;
                g_info.have3    = 1u;
                    g_info.seen_ms[2] = now_ms();
                if (t3r.fired3 && !prev_fired3) {
                    trace_al3_t a3 = {
                        .magic = TRACE_MAGIC_AL3, .frame = frame, .t_s = t,
                        .r_hz = g_t3st->r_on, .W = t3r.W, .hits = t3r.hits,
                        .n_events = (uint32_t)g_t3st->n_events + 1u};
                    trace_send_al3(&a3);
                    alerted_once = true;
                }
                prev_fired3 = t3r.fired3;
            }

            if (t4ran) {
                trace_text_t4(frame, &t4r);
                last_W4 = (float)t4r.W4;
                if (t4r.fired4 && !prev_fired4) {
                    alerted_once = true;
                }
                prev_fired4 = t4r.fired4 ? 1u : 0u;
            }

            if (disp_on && frame >= foot_next) {
                foot_next = frame + 32u;          /* about once a second */
                int alive = 0;
                for (int c = 0; c < GUARD_N_CH; c++) {
                    const float *w = g_gwin[c] + (CFG_N_FFT - CFG_HOP);
                    float acc = 0.0f;
                    for (int k = 0; k < CFG_HOP; k += 4) {   /* 1 in 4 is plenty */
                        acc += w[k] * w[k];
                    }
                    /* 1e-4 of full scale is ~3 int16 counts: below that a
                     * channel is not quiet, it is absent. */
                    if (sqrtf(acc / (float)(CFG_HOP / 4)) > 1e-4f) {
                        alive++;
                    }
                }
                /* ---- the ping tick ------------------------------------
                 * In the one-per-second block because that is the coarsest
                 * clock the protocol needs and the finest the radio should
                 * see: a ping is a range instrument, not an alert, and it
                 * must never contend with one. lora_link_send_test() queues
                 * on the link task, so nothing here waits on the air. */
                if (g_ping_period_s &&
                    (int32_t)(now_ms() - g_ping_due_ms) >= 0) {
                    g_ping_due_ms = now_ms() + g_ping_period_s * 1000u;
                    if (lora_link_send_test(true)) {
                        g_ping_tx++;
                    }
                }

                /* Integers only: PicoLibC's printf has no float support,
                 * which is why the whole trace is binary. Clamped so the
                 * compiler can see the field widths are bounded. */
                int thr_milli = (int)(thr * 1000.0 + 0.5);
                if (thr_milli < 0)     { thr_milli = 0; }
                if (thr_milli > 99999) { thr_milli = 99999; }

                /* ---- the operator display --------------------------------
                 *
                 * One snapshot per second, and epaper_set_main() throws away
                 * any that would draw the same pixels - so this loop is free
                 * on the ~86 000 seconds a day when nothing happens, and the
                 * panel redraws only when something did.
                 *
                 * The time fields are only refreshed on the hour, and that is
                 * the whole of the refresh budget's arithmetic. A "last alert
                 * 12 min ago" that ticked would be a two-second full-panel
                 * refresh every sixty seconds, for ever: 1440 a day against
                 * the ~30 this device is allowed. Between heartbeats the age
                 * is stale by up to an hour, which is what "coarse" means and
                 * is the right trade on a panel that costs two seconds to
                 * change. An event-driven publish - an alert, a battery
                 * slice, a warning - carries fresh time along with it for
                 * free, because it was going to redraw anyway. */
                const uint32_t hour = now_ms() / 3600000u;
                const bool beat = (hour != disp_hour);
                if (beat) {
                    disp_hour = hour;
                }

                /* HOME says LISTENING and nothing else. ALERT and SNOOZE are
                 * their own screens, so the resting screen never changes its
                 * own headline. */
                snprintf(disp.state_word, sizeof(disp.state_word),
                         "LISTENING");
                {
                    const int adb = ambient_db_now();
                    snprintf(disp.ambient, sizeof(disp.ambient), "%s",
                             ambient_word(adb, &amb_bucket));
                    amb_db = adb;
                }
                disp.snooze_s = (uint16_t)(SNOOZE_MS / 1000u);

                /* THE WARNING LINE. A fault an operator would otherwise have
                 * to know to look for. It is on MAIN and not on the status
                 * page for exactly that reason: nobody checks a status page
                 * to find out whether they should have checked it. */
                /* ---- the mic count is off this screen ------------------
                 * Put in the warning line it makes the home screen redraw
                 * constantly: every change is a full two-second refresh, and
                 * `alive` moves on ordinary variation, so the resting screen
                 * never rests.
                 *
                 * The count is not lost - INFO carries it as MIC n/4 OK/FAIL,
                 * which is where somebody checking the box will look. What is
                 * still owed is a once-only MIC FAULT chN report and its ring
                 * entry; without them a channel that dies overnight is
                 * visible only to whoever opens INFO.
                 *
                 * LOW BATT stays: it is a fact about the whole unit, it moves
                 * once, and it is the one thing an operator walking past must
                 * not have to open a page to discover. */
                if (power_mon_state() == POWER_LOW) {
                    snprintf(disp.warn, sizeof(disp.warn), "LOW BATT");
                } else {
                    disp.warn[0] = 0;
                }
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
void app_main(void)
{
    /* THE ONLY BOOT-PATH ADDITION IN THIS BUILD, and it is a safety default,
     * not a feature: the buzzer and motor sit behind NPN drivers whose bases
     * hang off GPIO17/18 through 1 kOhm, so a high-Z pad at reset is an
     * undefined base drive. Two GPIO writes, before anything else can take
     * time. Every other new peripheral (RMT, SPI/e-paper, button, I2S1)
     * initialises lazily on first use of its own command, so the path from
     * reset to a golden replay is otherwise byte-for-byte what it was. */
    actuators_boot_safe();

    /* ---- release the deep-sleep holds -----------------------------------
     *
     * OFF-DEEP latches GPIO16/17/18 low so the LED, the buzzer and the motor
     * cannot twitch while the chip sleeps. A latch survives the wake, so it
     * must be released here or every output stays frozen for the whole of the
     * next run and the device comes back silent and dark while insisting it
     * is guarding. Released unconditionally: calling these on a boot that
     * never slept is harmless, and a conditional would be one more thing to
     * get wrong. */
    gpio_deep_sleep_hold_dis();
    gpio_hold_dis((gpio_num_t)PIN_LED_WS2812);
    gpio_hold_dis((gpio_num_t)PIN_BUZZER);
    gpio_hold_dis((gpio_num_t)PIN_MOTOR);

    /* ---- SECTION 2.5: WHAT THE LAST BOOT DID ---------------------------
     * Called here, before anything else can take time, because it must read
     * the reset reason and the RTC blob before any later code can disturb
     * either. It PRINTS nothing: the USB serial driver is not up yet at this
     * point and an early trace_text is simply dropped, which is how the first
     * attempt at this lost its own boot line. The printing happens after
     * "STAGE1A READY" below. */
    s_boot_rtc_survived = bootrec_begin();

    /* THE LED'S SELF-HEALING RE-SEND. Started once, here, so it covers the
     * console as well as the guard: a pixel that mis-decodes a frame heals
     * within LED_REFRESH_MS instead of holding the wrong colour until the
     * next state change. Stopped again by alert_ui_power_down(), so a device
     * drawing OFF has nothing quietly re-lighting it. */
    (void)led_refresh_start();

    /* ---- THE SNOOZE BUTTON, SAMPLED ONCE AT BOOT ------------------------
     *
     * Read this before believing the result. A 500 ms window in which nobody
     * presses reads EXACTLY like an unwired pin, so this can report that it
     * saw no edge and it can NEVER report that the button is broken. That
     * distinction is not pedantry: a scan whose window opens before anybody
     * can press will call a working pin dead, and opening the serial port
     * resets the ESP32-S3, so that window is easy to miss. This print exists
     * so the question is answered by the board in front of you rather than by
     * a document. */
    {
        gpio_config_t bc = {
            .pin_bit_mask = 1ULL << PIN_SNOOZE_BTN,
            .mode = GPIO_MODE_INPUT,
            .pull_up_en = GPIO_PULLUP_ENABLE,
            .pull_down_en = GPIO_PULLDOWN_DISABLE,
            .intr_type = GPIO_INTR_DISABLE,
        };
        int lo = 1, seen = 0;
        if (gpio_config(&bc) == ESP_OK) {
            for (int i = 0; i < 100; i++) {
                if (gpio_get_level(PIN_SNOOZE_BTN) == 0) { lo = 0; seen = 1; }
                vTaskDelay(pdMS_TO_TICKS(5));
            }
        }
        (void)lo;
        trace_text(seen
            ? "SNOOZE_BTN: ok - saw the pin go low\n"
            : "SNOOZE_BTN: no press seen in 500 ms. This is NOT evidence the\n"
              "            pin is unwired - nobody may have pressed it. Hold\n"
              "            the button during boot, or use `U btn tap`.\n");
        /* Leave it as the ISR wants it; alert_ui's button_init() reconfigures
         * with the negedge interrupt on first use, and the idle state is the
         * same pulled-up input either way. */
    }

    /* The trace is binary and shares the link with the log. Silence the log
     * so a stray ESP_LOGx can never land inside a record. */
    esp_log_level_set("*", ESP_LOG_NONE);
    trace_link_init();
    vTaskDelay(pdMS_TO_TICKS(100));

    if (detector_init() != ESP_OK) {
        trace_text("FATAL esp-dsp fft init failed\n");
        return;
    }

    g_st = heap_caps_calloc(1, sizeof(detector_state_t), MALLOC_CAP_INTERNAL | MALLOC_CAP_8BIT);
    /* 16-byte alignment is REQUIRED, not preferred: dsps_fft2r_fc32 resolves
     * to the ESP32-S3 SIMD variant, whose 128-bit loads need it. malloc only
     * promises 4, and the aligned(16) attribute on a struct member does not
     * reach the allocator. */
    g_w = heap_caps_aligned_calloc(16, 1, sizeof(detector_work_t),
                                   MALLOC_CAP_INTERNAL | MALLOC_CAP_8BIT);
    /* g_block / g_q are NOT allocated here any more - see mono_alloc(). */
    if (!g_st || !g_w) {
        trace_text("FATAL out of internal RAM\n");
        return;
    }

    /* Tier-3's state, claimed before anything has fragmented the heap - but
     * ONLY if the stored pair wants it. Holding it unconditionally made the
     * v1+Tier-2 pair unallocatable; see t3_free(). run_standalone()
     * reconciles it on every run, so a pair switch needs no reboot. */
    if (settings_get()->t3_enabled && !t3_boot_alloc()) {
        trace_text("WARN Tier-3 unavailable: could not claim its state at "
                   "boot\n");
    }

    trace_text("\nSENTRY-NODE STAGE1A READY\n");

    /* THE BOOT RECORD, printed now that the link is actually up. */
    {
        char bb[192];
        /* THE PHASE IS ON THE BOOT LINE, not only in the record, because
         * during a 20-alert soak the console sees every reboot as it happens
         * and the record is exactly what a brownout throws away. */
        snprintf(bb, sizeof(bb), "BOOT reset=%s wake=%s rtc=%s phase=%s\n",
                 bootrec_reason_name(bootrec_reset_reason()),
                 bootrec_wake_name(bootrec_wake_cause()),
                 s_boot_rtc_survived ? "survived" : "INITIALISED",
                 bootrec_phase_name(bootrec_phase_at_reset()));
        trace_text(bb);
        if (s_boot_rtc_survived && bootrec_mirror_count() > 0u) {
            snprintf(bb, sizeof(bb),
                     "RING-MIRROR: %u entries survived reset %s\n",
                     (unsigned)bootrec_mirror_count(),
                     bootrec_reason_name(bootrec_reset_reason()));
            trace_text(bb);
        }
    }

    /* WHAT THIS WAKE HAS TO PROVE, before autostart takes it to LISTENING.
     * On any boot that is not a deep-sleep wake this only records the button
     * level and returns. */
    handle_deepsleep_wake();

    char line[64];

    /* ---- THE POWER-ON PATH ----------------------------------------------
     * autostart is a persisted setting and ships ON, so a board that comes up
     * on a charger starts guarding by itself. It is not a trap door: any host
     * line takes the console, WITH THE LINE INTACT (trace_try_line), and the
     * console then keeps it. That asymmetry is deliberate - a lab session must
     * be deterministic, so the guard never re-arms behind the operator's back.
     * `S` puts it back. */
    bool console = false;
    int  fail_streak = 0;

    for (;;) {
        if (!console && settings_get()->autostart) {
            const int why = run_standalone();

            /* THE TWO HONEST ENDINGS. Both leave the panel saying OFF with
             * the reason under it, and both stop the device. On a board that
             * deep-sleeps neither call returns at all; on the breadboard they
             * park in standby and come back when the button is pressed, which
             * is the same `continue` the long press takes. */
            if (why == RUN_END_POWER || why == RUN_END_BATTERY) {
                /* On a board that deep-sleeps this never returns. On the
                 * breadboard it parks against the OFF screen it just drew and
                 * comes back when the button is pressed, which is why the
                 * pending-line handling below is shared. */
                run_off_and_sleep(
                    why == RUN_END_BATTERY
                        ? "BATTERY EMPTY - CHARGE ME"
                        : (BOARD_SLIDE_HARD_CUT
                               ? "HOLD 2 s OR SLIDE THE SWITCH NOW"
                               : "SAFE TO UNPLUG"),
                    why == RUN_END_BATTERY);
            }
            if (why == RUN_END_POWER || why == RUN_END_BATTERY) {
                if (g_have_pending) {
                    g_have_pending = false;
                    console = true;
                    dispatch_line(g_pending);
                    if (g_want_standalone) {
                        g_want_standalone = false;
                        console = false;
                        fail_streak = 0;
                    }
                }
                continue;                 /* the button woke it: guard again */
            }
            if (why == RUN_END_INPUT && g_have_pending) {
                g_have_pending = false;
                console = true;
                dispatch_line(g_pending);
                if (g_want_standalone) {
                    g_want_standalone = false;
                    console = false;
                    fail_streak = 0;
                }
                continue;
            }
            /* It could not start - no I2S, or no RAM. Retry a few times,
             * because a field device that gives up on the first transient is
             * a field device that comes home with no data, then stop and say
             * so rather than spin a fault at 30 Hz forever. */
            if (++fail_streak >= 5) {
                trace_text("SENTRY standalone could not start 5 times; "
                           "console only. Fix the fault and send S.\n");
                console = true;
                continue;
            }
            for (int i = 0; i < 30 && !console; i++) {
                if (trace_try_line(g_pending, sizeof(g_pending)) > 0) {
                    g_have_pending = false;
                    console = true;
                    dispatch_line(g_pending);
                    break;
                }
                alert_ui_idle_led(true, now_ms());
                vTaskDelay(pdMS_TO_TICKS(100));
            }
            continue;
        }

        int n = trace_read_line(line, sizeof(line), portMAX_DELAY);
        if (n <= 0) {
            continue;
        }
        /* `S` hands the device back to itself: the console releases it and the
         * guard restarts from the persisted settings. It is how a bench
         * session ends without a power cycle, and it is the only way back into
         * standalone once a host has spoken. dispatch_line() owns the letter;
         * this loop only acts on the flag it sets. */
        dispatch_line(line);
        if (g_want_standalone) {
            g_want_standalone = false;
            console = false;
            fail_streak = 0;
        }
    }
}
